Belprot/2230_TubePitotDeporte_v1.0.0/doc/Annexes/Mode d'emploi.pdf

## Mode d’emplois :

1. Branchez le connecteur de la baterie.
2. Vissez le support pile au boier principale.
3. Allumez le système à l’aide du switch.
4. Appairez le système à l’appareil Android.
5. Lancez l’applicaon dédiée.
