Belprot/2230_TubePitotDeporte_v1.0.0/doc/Annexes/Code/app.c.pdf

1 /******************************************************************************* 2 MPLAB Harmony Application Source File
3
4 | Company:
5 | Microchip Technology Inc.
6
7 | File Name:
8 | app.c
9
10 | Summary:
11 | This file contains the source code for the MPLAB Harmony application.
12
13 | Description:
14 | This file contains the source code for the MPLAB Harmony application. It
15 | implements the logic of the application's state machine and it may call
16 | API routines of other MPLAB Harmony modules in the system, such as drivers,
17 | system services, and middleware. However, it does not call any of the
18 | system interfaces (such as the "Initialize" and "Tasks" functions) of any of
19 | the modules in the system or make any assumptions about when those functions
20 | are called. That is the responsibility of the configuration-specific system
21 | files.
22 *******************************************************************************/ 23
24 // DOM-IGNORE-BEGIN
25 /******************************************************************************* 26 Copyright (c) 2013-2014 released Microchip Technology Inc. All rights reserved. 27
28 Microchip licenses to you the right to use, modify, copy and distribute
29 Software only when embedded on a Microchip microcontroller or digital signal 30 controller that is integrated into your product or third party product
31 (pursuant to the sublicense terms in the accompanying license agreement). 32
33 You should refer to the license agreement accompanying this Software for
34 additional information regarding your rights and obligations.
35
36 SOFTWARE AND DOCUMENTATION ARE PROVIDED "AS IS" WITHOUT WARRANTY OF ANY KIND, 37 EITHER EXPRESS OR IMPLIED, INCLUDING WITHOUT LIMITATION, ANY WARRANTY OF
38 MERCHANTABILITY, TITLE, NON-INFRINGEMENT AND FITNESS FOR A PARTICULAR PURPOSE. 39 IN NO EVENT SHALL MICROCHIP OR ITS LICENSORS BE LIABLE OR OBLIGATED UNDER
40 CONTRACT, NEGLIGENCE, STRICT LIABILITY, CONTRIBUTION, BREACH OF WARRANTY, OR 41 OTHER LEGAL EQUITABLE THEORY ANY DIRECT OR INDIRECT DAMAGES OR EXPENSES
42 INCLUDING BUT NOT LIMITED TO ANY INCIDENTAL, SPECIAL, INDIRECT, PUNITIVE OR 43 CONSEQUENTIAL DAMAGES, LOST PROFITS OR LOST DATA, COST OF PROCUREMENT OF
44 SUBSTITUTE GOODS, TECHNOLOGY, SERVICES, OR ANY CLAIMS BY THIRD PARTIES
45 (INCLUDING BUT NOT LIMITED TO ANY DEFENSE THEREOF), OR OTHER SIMILAR COSTS.
46 *******************************************************************************/ 47 // DOM-IGNORE-END
48

49
50 // Author M.Ricchieri
51
52
53 // ***************************************************************************** 54 // ***************************************************************************** 55 // Section: Included Files
56 // ***************************************************************************** 57 // ***************************************************************************** 58
59 #include "app.h"
60 #include "Mc32_I2cUtilCCS.h"
61
62 #include "HSCMRRN001PD2A3_driver.h" 63
64 #include "RN4678_driver.h"
65 #include "voltageADC_driver.h"
66
67
68
69 // ***************************************************************************** 70 // ***************************************************************************** 71 // Section: Global Data Definitions
72 // ***************************************************************************** 73 // *****************************************************************************
74

## C:/microchip/harmony/v2_06/apps/PROJ/2230_TubePitotDeporte_v1.0.0/firmware/src/app.c

1.1 of 6 | 2023.06.16 03:15:27

75 //----------------------------------------------------------------------------// Global data
76 APP_DATA | appData;
77 SENS_DATA | sensData;
78
79 struct inv_imu_device | myImuDevice;
80 struct inv_imu_serif | myImuSertif;
81
82
83
84 // ***************************************************************************** 85 // ***************************************************************************** 86 // Section: Application Callback Functions
87 // *****************************************************************************
88 // *****************************************************************************
89
90 ////----------------------------------------------------------------------------// TIMER0 callback function <--- Disabled 91 //void TIMER0_Callback_Function(){ //156Hz
92 //
93 // // xxxx
94 //}
95
96

97 //----------------------------------------------------------------------------// TIMER1 callback function 98 void TIMER1_Callback_Function(){ // 20Hz
99
100 // if(appData.isBluetoothDiscoverable){
101 //
102 // | if(inv_imu_get_time_us() >= 120000000){ // 120 000 000 = 120 seconds
103 //
104 // | turnOffDiscoverBT();
105 // | appData.isBluetoothDiscoverable = false;
106 // | }
107 // | }
108 | // Update the main state machine
109 | APP_UpdateAppState(APP_STATE_SERVICE);
110 }
111
112
113 //----------------------------------------------------------------------------// USART1_Callback_Function 114 void USART1_Callback_Function(void){
115
116 | char a_received[50];
117 | char* result;
118
119 | // Gets new data from FIFO
120 | getUsartData(&a_received[0]);
121
122 | // If "<RFCOMM_OPEN>" is present in the array received
123 | result = strstr(a_received, "<RFCOMM_OPEN>");
124 | if(result != NULL){
125
126 | appData.isBluetoothDiscoverable = false;
127 | appData.isBluetoothConnected = true;
128 | }
129
130 | // If "<RFCOMM_CLOSE>" is present in the array received
131 | result = strstr(a_received, "<RFCOMM_CLOSE>");
132 | if(result != NULL){
133
134 | // turnOnDiscoverBT();
135 | appData.isBluetoothConnected = false;
136 | }
137
138 // | // If "<xxxxxx>" is present in the array received
139 // | result = strstr(a_received, "<xxxxxx>");
140 // | if(result != NULL){
141 //
142 // | // Does something
143 // | }
144 }

145
146
147 //----------------------------------------------------------------------------// IMU callback function 148 void imu callback(inv imu sensor eventt *event){

_ | ( | _ | _ | _ | _ | ){

// Transforms 16bits values into degrees and saves them in the sensor data // structure
// 250 dps
sensData.gyroX = (event->gyro[0])/250 + 1; // + offset
sensData.gyroY = (event->gyro[1])/250 + 1; // + offset sensData.gyroZ = (event->gyro[2])/250;

// Reads and transforms 16bits values into
// Transforms 16bits values into g acceleration and saves them in the sensor // data structure (8192 bits per g)
sensData.accelX = (float)(event->accel[0])/8192.0;
sensData.accelY = (float)(event->accel[1])/8192.0;
sensData.accelZ = (float)(event->accel[2])/8192.0 + 0.075; // + offset

// Calculate the angle with the gyro values
// 0.05 correspond to the period between each reading 1/20Hz = 0.05s sensData.GyrAngleX += sensData.gyroX * 0.05;
sensData.GyrAngleY += sensData.gyroY * 0.05;
sensData.GyrAngleZ += sensData.gyroZ * 0.05;
169 }

172 // ***************************************************************************** 173 // ***************************************************************************** 174 // Section: Application Local Functions
175 // *****************************************************************************
176 // *****************************************************************************

178 //----------------------------------------------------------------------------// APP_UpdateAppState 179 void APP_UpdateAppState(APP_STATES newState){

appData.appState = newState;
182 }

185 //----------------------------------------------------------------------------// APP_UpdateServiceState 186 void APP_UpdateServiceState(SERVICE_STATES newState){

appData.serviceState = newState;
189 }

192 //----------------------------------------------------------------------------// clearArray

193 void clearArray(size_t arraySize, char *pArrayToClear){

int i;

for (i = 0; i < arraySize; i++){

pArrayToClear[i] = NULL;
}
201 }

204 //----------------------------------------------------------------------------// frameFormatting 205 inline void frameFormatting(char* a_dataToSend, const SENS_DATA* sensData){

// Saves all data into a simple frame
// Speed in [km/h]
// Gyros in [dps]
// Angles in [degrees]
// Accelerations in [g]
// VB and VG in [V]
sprintf(a_dataToSend, "S=%03d GX=%+.02f GY=%+.02f GZ=%+.02f GAX=%+.02f " "GAY=%+.02f GAZ=%+.02f AX=%+.02f AY=%+.02f AZ=%+.02f VB=%.02f " "VG=%.02f\n\r",
sensData->velocity,
sensData->gyroX, sensData->gyroY, sensData->gyroZ, sensData->GyrAngleX, sensData->GyrAngleY, sensData->GyrAngleZ, sensData->accelX, sensData->accelY, sensData->accelZ, sensData->batVoltage, sensData->genVoltage);
221 }

223 // ***************************************************************************** 224 // ***************************************************************************** 225 // Section: Application Initialization and State Machine Functions
226 // *****************************************************************************
227 // *****************************************************************************
228
229 //----------------------------------------------------------------------------// APP_Initialize 230 void APP_Initialize(void){
231
232 // Initializes the appData structure
233
234 | appData.appState | = APP_STATE_INIT;
235 | appData.isBluethoothModuleInit = false;
236 | appData.isBluetoothConnected | = false;
237 | appData.isBluetoothDiscoverable = false;
238 | sensData.GyrAngleX = 0;
239 | sensData.GyrAngleY = 0;
240 | sensData.GyrAngleZ = 0;

241 }
242
243
244 //----------------------------------------------------------------------------// initImuInterface 245 // Initialize serial interface between MCU and IMU
246 int initImuInterface(struct inv_imu_serif *icm_serif){
247
248 | // No need
249 icm_serif->context | = 0;
250 | // Points to the reading function dedicated
251 icm_serif->read_reg | = ICM42670P_I2C_bus_read;
252 | // Points to the writing function dedicated
253 icm_serif->write_reg = ICM42670P_I2C_bus_write;
254 icm_serif->max_read = 255; /* maximum number of bytes allowed per serial read */ 255 icm_serif->max_write = 255; /* maximum number of bytes allowed per serial write */ 256 // Set the communication interface
257 icm_serif->serif_type = SERIF_TYPE;
258
259 return 0;
260 }
261
262
263 //----------------------------------------------------------------------------// APP_Tasks 264 void APP_Tasks(void){
265
266 RAW_ADC rawAdc;
267
268 | // Check the application's current state
269 | switch(appData.appState){
270
271 | // Application's initial state
272 | case APP_STATE_INIT:
273 | {
274 | int rc = 0;
275
276 | // Initialization of the I2C communication
277 | i2c_init(SLOW);
278
279 | do{
280 | // Initialization of the ICM42670 interface
281 | rc |= initImuInterface(&myImuSertif);
282 | // Resets and prepares the chip for the configuration
283 | rc |= setupImuDevice(&myImuSertif);
284 | // Configures ICM42670 parameters
285 | rc |= configureImuDevice();
286
287 | }while(rc != INV_ERROR_SUCCESS);
288
289 | // Initialization of the USART FIFOs
290 | initFifo(&usartFifoRx, FIFO_RX_SIZE, a_fifoRx, 0);
291 | initFifo(&usartFifoTx, FIFO_TX_SIZE, a_fifoTx, 0);
292
293 | do{
294 | // Initialization of the Bluetooth module
295 | appData.isBluethoothModuleInit = init_RN4678();
296

}while(appData.isBluethoothModuleInit == false);

// Initialization of the ADC module
initAdc();

// Starts TIMERs
303 // | DRV_TMR0_Start(); <--- Disabled
| DRV_TMR1_Start();
| DRV_TMR2_Start();
| // States machines update
| APP_UpdateAppState(APP_STATE_WAIT);
| APP_UpdateServiceState(SERVICE_STATE_READ_SENSORS);
| break;
}
| case APP_STATE_SERVICE:
{
| int8_t a_frameToSend[130];
| switch(appData.serviceState){
| case SERVICE_STATE_READ_SENSORS:
| // Reads voltages values
| readRawAdc(&rawAdc);
| convertRawToVoltage(&rawAdc, &sensData);
| // Reads velocity value
| convertRawToVelocity(readRawDiffPress(), &sensData);
| // Gets new IMU data
| get_imu_data();

APP_UpdateServiceState(SERVICE_STATE_PROCESS); break;

case SERVICE_STATE_PROCESS:

// Clears the array before saving new values

clearArray(sizeof(a_frameToSend), (char*)&a_frameToSend[0]); // Converts float values in a char array (frame) frameFormatting((char*)&a_frameToSend[0], &sensData);

APP_UpdateServiceState(SERVICE_STATE_SEND_DATA_BT); break;

case SERVICE_STATE_SEND_DATA_BT:

// Bluetooth is connected to a device if(appData.isBluetoothConnected == true){

// Sends frame through USART sendData_RN4678(&a_frameToSend[0]); // Toggle signalisation LED SIGN_LEDToggle();
}
else SIGN_LEDOn();

APP_UpdateAppState(APP_STATE_WAIT); APP_UpdateServiceState(SERVICE_STATE_READ_SENSORS); break;
}
break;
}

case APP_STATE_WAIT:
{
// Does nothing here
break;
}
default:
{
// Does nothing here

370 | // Does nothing here
371 | break;
372 | }
373 | }
374 }
375
376
377 /******************************************************************************* 378 End of File
379 */
