Belprot/2230_TubePitotDeporte_v1.0.0/doc/Annexes/Code/HSCMRRN001PD2A3_driver.c.pdf

1 /*
2 * File: HSCMRRN001PD2A3_driver.c 3 * Author: M.Ricchieri
4 *
5 * Created on 12. avril 2023
6 */

9 //----------------------------------------------------------------------------// Includes 10 #include "HSCMRRN001PD2A3_driver.h"
11 #include "math.h"
12 #include "Mc32_I2cUtilCCS.h"
13 #include "peripheral\i2c\plib_i2c.h"

16 //----------------------------------------------------------------------------// Constants 17 #define HSCMRRN001PD2A3_ADDR 0x51

19 #define RHO_AIR 1.2

22 //----------------------------------------------------------------------------// readRawDiffPress 23 // Read the raw compensed differential pressure from the HSCMRRN001PD2A3 sensor
24 int16_t readRawDiffPress(){

int16_t rawDiffPress;
uint8_t MSB;
uint8_t LSB;

// I2C communication with the sensor i2c_start();
i2c_write(HSCMRRN001PD2A3_ADDR);
MSB = i2c_read(1);
LSB = i2c_read(1);
// Reads 2 unused bytes to avoid bug // needs to be clarified ! i2c_read(1);
i2c_read(0); // No ACK
i2c_stop();

// Data formatting
rawDiffPress = MSB;
rawDiffPress = rawDiffPress << 8;
rawDiffPress = rawDiffPress | LSB;
rawDiffPress = rawDiffPress - 8192; // Safety to avoid negative speeds if(rawDiffPress < 0) rawDiffPress = 0;

return rawDiffPress;

49 }

52 //----------------------------------------------------------------------------// convertRawToVelocity 53 // Convert raw compensed differential pressure to velocity (km/h))
54 void convertRawToVelocity(int16_t rawDiffPress, SENS_DATA *pSensData){

// Multiplied by 3.6 to obtain velocity in km/h instead of m/s pSensData->velocity = 3.6 * (sqrtf((2*(float)rawDiffPress)/(RHO_AIR))); 58 }

C:/microchip/harmony/v2_06/apps/PROJ/2230_TubePitotDeporte_v1.0.0/firmware/src/HSCMRRN001PD2A3_driver.c

1.1 of 1 | 2023.06.15 00:41:27
