Belprot/2230_TubePitotDeporte_v1.0.0/doc/Annexes/Code/I2C_ICM42670P_Functions.c.pdf

2 /*
3 * File: I2C_ICM42670P_Function.c 4 * Author: M.Ricchieri
5 *
6 * Created on 10. mai 2023
7 *
8 * This code uses the Mc32_I2cUtilCCS.h 9 */

12 //----------------------------------------------------------------------------// Includes 13 #include "stdint.h"
14 #include "Mc32_I2cUtilCCS.h"
15 #include "imu/inv_imu_driver.h"
16 #include "imu/inv_imu_transport.h" 17 #include "I2C_ICM42670P_Functions.h"

20 //----------------------------------------------------------------------------// Constants 21 #define ICM42670P_INIT_VALUE 0
22 #define I2C_BUFFER_LEN 10
23 #define ICM42670P_I2C_BUS_WRITE_ARRAY_INDEX 1

26 // \Brief : Those functions are used by the ICM42670 IMU to communicate with
27 // | the chip in I2C. The first one is used to read and the second to
28 // | write in the chip. Those functions are pointed by the ICM42670
29 // | driver.

31 //----------------------------------------------------------------------------// ICM42670P_I2C_bus_write 32 int ICM42670P_I2C_bus_write(struct inv_imu_serif *serif, uint8_t reg,
| const uint8_t *buf, uint32_t len){
| int cursor = 0;
| i2c_start();
| i2c_write(ICM42670P_ADDR_W);
| i2c_write(reg);
| for (cursor = 0; cursor < len; cursor++){
| i2c_write(*(buf+cursor));
}
| i2c_stop();
| return 0;
48 }

51 //----------------------------------------------------------------------------// ICM42670P_I2C_bus_read 52 int ICM42670P_I2C_bus_read(struct inv_imu_serif *serif, uint8_t reg,
uint8_t *buf, uint32_t len){

uint8_t array[len];
int cursor = 0;

i2c_start();
i2c_write(ICM42670P_ADDR_W); i2c_write(reg);
i2c_start();
i2c_write(ICM42670P_ADDR_R);

for (cursor = 0; cursor < len; cursor++){

if((cursor+1) < len)
// With ACK
array[cursor] = i2c_read(1); else
// Without ACK
array[cursor] = i2c_read(0);

buf[cursor] = array[cursor]; //*(buf+cursor) = array[cursor];

C:/microchip/harmony/v2_06/apps/PROJ/2230_TubePitotDeporte_v1.0.0/firmware/src/I2C_ICM42670P_Functions.c

1.1 of 2 | 2023.06.15 00:41:27

75 | }
76 | i2c_stop();
77
78 return 0;
79 }

C:/microchip/harmony/v2_06/apps/PROJ/2230_TubePitotDeporte_v1.0.0/firmware/src/I2C_ICM42670P_Functions.c

2.1 of 2 | 2023.06.15 00:41:27
