Belprot/2230_TubePitotDeporte_v1.0.0/doc/Annexes/Code/TerminalFragment.java.pdf

1 | package de.kai_morich.simple_bluetooth_terminal;
3 | import android.annotation.SuppressLint;
4 | import android.app.Activity;
5 | import android.app.AlertDialog;
6 | import android.bluetooth.BluetoothAdapter;
7 | import android.bluetooth.BluetoothDevice;
8 | import android.content.ComponentName;
9 | import android.content.Context;
10 | import android.content.Intent;
11 | import android.content.ServiceConnection;
12 | import android.os.Bundle;
13 | import android.os.IBinder;
14 | import android.text.Spannable;
15 | import android.text.SpannableStringBuilder;
16 | import android.text.style.ForegroundColorSpan;
17 | import android.view.LayoutInflater;
18 | import android.view.Menu;
19 | import android.view.MenuInflater;
20 | import android.view.MenuItem;
21 | import android.view.View;
22 | import android.view.ViewGroup;
23 | import android.widget.TextView;
24 | import android.widget.Toast;
25
26 | import androidx.annotation.NonNull;
27 | import androidx.annotation.Nullable;
28 | import androidx.fragment.app.Fragment;
29
30 | import java.util.ArrayDeque;
31 | import static java.lang.Math.*;
32
33
34
35 | public class TerminalFragment extends Fragment implements ServiceConnection,
SerialListener {
36
37 | private enum Connected { False, Pending, True }
38
39 | private String deviceAddress;
40 | private SerialService service;
41
42 | //private TextView receiveText;
43
44 | private TextView speedText;
45 | private TextView gyroXText;
46 | private TextView gyroYText;
47 | private TextView gyroZText;
48 | private TextView anglGyrXText;
49 | private TextView anglGyrYText;
50 | private TextView anglGyrZText;
51 | private TextView accelXText;
52 | private TextView accelYText;
53 | private TextView accelZText;
54 | private TextView vbatText;
55 | private TextView vgenText;
56 | private TextView pitchText;
57 | private TextView yawText;
58 | private TextView rollText;
59
60
61 | private TextView sendText;
62 | private TextUtil.HexWatcher hexWatcher;
64 | private Connected connected = Connected.False;
65 | private boolean initialStart = true;

66 | private boolean hexEnabled = false;
67 | private boolean pendingNewline = false;
68 | private String newline = TextUtil.newline_crlf;
70 | // Personal variables
71 | public double sValue = 0.0;
72 | public double gxValue = 0.0;
73 | public double gyValue = 0.0;
74 | public double gzValue = 0.0;
75 | public double gaxValue = 0.0;
76 | public double gayValue = 0.0;
77 | public double gazValue = 0.0;
78 | public double axValue = 0.0;
79 | public double ayValue = 0.0;
80 | public double azValue = 0.0;
81 | public double vbatValue = 0.0;
82 | public double vgenValue = 0.0;
83
84 | /*
85 | * Lifecycle
86 | */
87 | @Override
88 | public void onCreate(@Nullable Bundle savedInstanceState){
89 | super.onCreate(savedInstanceState);
90 | setHasOptionsMenu(true);
91 | setRetainInstance(true);
92 | deviceAddress = getArguments().getString("device");
93 | }
94
95 | @Override
96 | public void onDestroy() {
97 | if (connected != Connected.False)
98 | disconnect();
99 | getActivity().stopService(new Intent(getActivity(), SerialService.class));
100 | super.onDestroy();
101 | }
102
103 | @Override
104 | public void onStart() {
105 | super.onStart();
106 | if(service != null)
107 | service.attach(this);
108 | else
109 | getActivity().startService(new Intent(getActivity(), SerialService.class));
| // prevents service destroy on unbind from recreated activity caused by
| orientation change
110 | }
111
112 | @Override
113 | public void onStop() {
114 | if(service != null && !getActivity().isChangingConfigurations())
115 | service.detach();
116 | super.onStop();
117 | }
118
119 | @SuppressWarnings("deprecation") // onAttach(context) was added with API 23.
| onAttach(activity) works for all API versions
120 | @Override
121 | public void onAttach(@NonNull Activity activity){
122 | super.onAttach(activity);
123 | getActivity().bindService(new Intent(getActivity(), SerialService.class), this,
| Context.BIND_AUTO_CREATE);
126 | @Override
127 | public void onDetach() {

128 | try { getActivity().unbindService(this); } catch(Exception ignored) {}
129 | super.onDetach();
132 | @Override
133 | public void onResume() {
134 | super.onResume();
135 | if(initialStart && service != null){
136 | initialStart = false;
137 | getActivity().runOnUiThread(this::connect);
138 | }
139 | }
140
141 | @Override
142 | public void onServiceConnected(ComponentName name, IBinder binder){
143 | service = ((SerialService.SerialBinder) binder).getService();
144 | service.attach(this);
145 | if(initialStart && isResumed()) {
146 | initialStart = false;
147 | getActivity().runOnUiThread(this::connect);
148 | }
149 | }
150
151 | @Override
152 | public void onServiceDisconnected(ComponentName name){
153 | service = null;
154 | }
155
156 | /*
157 | * UI
158 | */
159 | @Override
160 | public View onCreateView(@NonNull LayoutInflater inflater, ViewGroup container,
| Bundle savedInstanceState){
161 | View view = inflater.inflate(R.layout.fragment_terminal, container, false);
162 | // Assignment text to textView
163 | speedText = view.findViewById(R.id.speed_viewer);
164 | gyroXText = view.findViewById(R.id.gyroX_viewer);
165 | gyroYText = view.findViewById(R.id.gyroY_viewer);
166 | gyroZText = view.findViewById(R.id.gyroZ_viewer);
167 | anglGyrXText = view.findViewById(R.id.angGyrX_viewer);
168 | anglGyrYText = view.findViewById(R.id.angGyrY_viewer);
169 | anglGyrZText = view.findViewById(R.id.angGyrZ_viewer);
170 | accelXText = view.findViewById(R.id.accelX_viewer);
171 | accelYText = view.findViewById(R.id.accelY_viewer);
172 | accelZText = view.findViewById(R.id.accelZ_viewer);
173 | vbatText = view.findViewById(R.id.vbat_viewer);
174 | vgenText = view.findViewById(R.id.vgen_viewer);
175 | pitchText = view.findViewById(R.id.pitch_viewer);
176 | yawText = view.findViewById(R.id.yaw_viewer);
177 | rollText = view.findViewById(R.id.roll_viewer);
178
179 | //receiveText = view.findViewById(R.id.receive_text);
| // TextView performance decreases with number of spans
180 | //receiveText.setTextColor(getResources().getColor(R.color.colorRecieveText));
| // set as default color to reduce number of spans
181 | //receiveText.setMovementMethod(ScrollingMovementMethod.getInstance());
182
183 | sendText = view.findViewById(R.id.send_text);
184 | hexWatcher = new TextUtil.HexWatcher(sendText);
185 | hexWatcher.enable(hexEnabled);
186 | sendText.addTextChangedListener(hexWatcher);
187 | sendText.setHint(hexEnabled ? "HEX mode" : "");
189 | View sendBtn = view.findViewById(R.id.send_btn);
190 | sendBtn.setOnClickListener(v -> send(sendText.getText().toString()));

191 | return view;
194 | @Override
195 | public void onCreateOptionsMenu(@NonNull Menu menu, MenuInflater inflater){
196 | inflater.inflate(R.menu.menu_terminal, menu);
197 | menu.findItem(R.id.hex).setChecked(hexEnabled);
198 | }
199
200 | @Override
201 | public boolean onOptionsItemSelected(MenuItem item){
202 | int id = item.getItemId();
203 | if (id == R.id.clear){
204 | //receiveText.setText("");
205 | return true;
206 | } else if (id == R.id.newline){
207 | String[] newlineNames = getResources().getStringArray(R.array.newline_names);
208 | String[] newlineValues = getResources().getStringArray(R.array.newline_values
| );
209 | int pos = java.util.Arrays.asList(newlineValues).indexOf(newline);
210 | AlertDialog.Builder builder = new AlertDialog.Builder(getActivity());
211 | builder.setTitle("Newline");
212 | builder.setSingleChoiceItems(newlineNames, pos,(dialog, item1) -> {
213 | newline = newlineValues[item1];
214 | dialog.dismiss();
215 | });
216 | builder.create().show();
217 | return true;
218 | } else if (id == R.id.hex){
219 | hexEnabled =!hexEnabled;
220 | sendText.setText("");
221 | hexWatcher.enable(hexEnabled);
222 | sendText.setHint(hexEnabled ? "HEX mode" : "");
223 | item.setChecked(hexEnabled);
224 | return true;
225 | } else {
226 | return super.onOptionsItemSelected(item);
227 | }
228 | }
229
230 | /*
231 | * Serial + UI
232 | */
233 | private void connect() {
234 | try {
235 | BluetoothAdapter bluetoothAdapter = BluetoothAdapter.getDefaultAdapter();
236 | BluetoothDevice device = bluetoothAdapter.getRemoteDevice(deviceAddress);
237 | status("connecting...");
238 | connected = Connected.Pending;
239 | SerialSocket socket = new SerialSocket(getActivity().getApplicationContext(),
| device);
240 | service.connect(socket);
241 | } catch (Exception e){
242 | onSerialConnectError(e);
243 | }
244 | }
245
246 | private void disconnect() {
247 | connected = Connected.False;
248 | service.disconnect();
249 | }
250
251 | private void send(String str){
252 | if(connected != Connected.True){
253 | Toast.makeText(getActivity(), "not connected", Toast.LENGTH_SHORT).show();
254 | return;

256 | try {
257 | String msg;
258 | byte[] data;
259 | if(hexEnabled){
260 | StringBuilder sb = new StringBuilder();
261 | TextUtil.toHexString(sb, TextUtil.fromHexString(str));
262 | TextUtil.toHexString(sb, newline.getBytes());
263 | msg = sb.toString();
264 | data = TextUtil.fromHexString(msg);
265 | } else {
266 | msg = str;
267 | data =(str + newline).getBytes();
268 | }
269 | SpannableStringBuilder spn = new SpannableStringBuilder(msg + '\n');
270 | spn.setSpan(new ForegroundColorSpan(getResources().getColor(R.color.
| colorSendText)), 0, spn.length(), Spannable.SPAN_EXCLUSIVE_EXCLUSIVE);
271 | //receiveText.append(spn);
272 | service.write(data);
273 | } catch (Exception e){
274 | onSerialIoError(e);
275 | }
276 | }
277
278 | @SuppressLint("SetTextI18n")
279 | private void receive(ArrayDeque<byte[]> datas){
280 | SpannableStringBuilder spn = new SpannableStringBuilder();
281 | for (byte[] data : datas){
282 | if (hexEnabled){
283 | spn.append(TextUtil.toHexString(data)).append('\n');
284 | } else {
285 | String msg = new String(data);
286 | if (newline.equals(TextUtil.newline_crlf) && msg.length() > 0){
287 | // don't show CR as ^M if directly before LF
288 | msg = msg.replace(TextUtil.newline_crlf, TextUtil.newline_lf);
289 | // special handling if CR and LF come in separate fragments
290 | if (pendingNewline && msg.charAt(0) == '\n'){
291 | if (spn.length() >= 2){
292 | spn.delete(spn.length() - 2, spn.length());
293 | } else {
294 | //Editable edt = receiveText.getEditableText();
295 | //if (edt != null && edt.length() >= 2)
296 | // edt.delete(edt.length() - 2, edt.length());
297 | }
298 | }
299 | pendingNewline = msg.charAt(msg.length() - 1) == '\r';
300 | }
301 | spn.append(TextUtil.toCaretString(msg, newline.length() != 0));
302 | }
303 | }
304
| //-------------------------------------------------------------------------------
| ---------// PERSONAL
305
306 | String[] pairs = spn.toString().split("\\s+"); | // Séparer la chaîne en paires
| clé-valeur
307
308 | for (String pair : pairs){
309 | String[] parts = pair.split("="); // Séparer chaque paire clé-valeur
310
311 | if (parts.length == 2){
312 | String key = parts[0];
313 | String valueStr = parts[1];
315 | try {
316 | double value = Double.parseDouble(valueStr);

318 | switch (key){
319 | case "S":
320 | sValue = value;
321 | break;
322 | case "GX":
323 | gxValue = value;
324 | break;
325 | case "GY":
326 | gyValue = value;
327 | break;
328 | case "GZ":
329 | gzValue = value;
330 | break;
331 | case "GAX":
332 | gaxValue = value;
333 | break;
334 | case "GAY":
335 | gayValue = value;
336 | break;
337 | case "GAZ":
338 | gazValue = value;
339 | break;
340 | case "AX":
341 | axValue = value;
342 | break;
343 | case "AY":
344 | ayValue = value;
345 | break;
346 | case "AZ":
347 | azValue = value;
348 | break;
349 | case "VB":
350 | vbatValue = value;
351 | break;
352 | case "VG":
353 | vgenValue = value;
354 | break;
355
356 | }
357 | } catch (NumberFormatException e){
358 | | // Gérer l'exception si la valeur n'est pas un nombre décimal valide
359 | }
360 | }
361 | }
362
363
364 | speedText.setText( "SPEED : " + String.valueOf(sValue)+ " km/h");
365 | gyroXText.setText( "GYRO X : " + String.valueOf(gxValue)+ " dps");
366 | gyroYText.setText( "GYRO Y : " + String.valueOf(gyValue)+ " dps");
367 | gyroZText.setText( "GYRO Z : " + String.valueOf(gzValue)+ " dps");
368 | anglGyrXText.setText("ANGL GYR X : " + String.valueOf(gaxValue)+ " °");
369 | anglGyrYText.setText("ANGL GYR Y : " + String.valueOf(gayValue)+ " °");
370 | anglGyrZText.setText("ANGL GYR Z : " + String.valueOf(gazValue)+ " °");
371 | accelXText.setText( "ACCEL X : " + String.valueOf(axValue)+ " g");
372 | accelYText.setText( "ACCEL Y : " + String.valueOf(ayValue)+ " g");
373 | accelZText.setText( "ACCEL Z : " + String.valueOf(azValue)+ " g");
374 | vbatText.setText( "VBAT : " + String.valueOf(vbatValue)+ " V");
375 | vgenText.setText( "VGEN : " + String.valueOf(vgenValue)+ " V");
376
377 | // Calculation of angles
378 | //pitchValue = Math.atan(axValue/(Math.sqrt(Math.pow(ayValue, 2) +
| Math.pow(azValue, 2))));
380 | //double angle = atan2(ayValue, axValue); // Calcul de l'angle en radians

382 | //double angle = atan(axValue/ayValue);
383 | // Conversion de l'angle en degrés et en float
384 | //float pitchValue = (float) toDegrees(angle);
386 | // Calcul des angles
387 | double roll = Math.atan2(ayValue, azValue);
388 | double pitch = Math.atan2(-axValue, Math.sqrt(ayValue * ayValue + azValue *
| azValue));
389 | double yaw = Math.atan2(Math.sin(roll)* axValue - Math.cos(roll)* ayValue, Math
| .cos(roll)* azValue);
390
391 | // Conversion des angles en degrés
392 | //roll = Math.toDegrees(roll);
393 | pitch = Math.toDegrees(pitch);
394 | yaw = Math.toDegrees(yaw);
395
396 | pitchText.setText( "PITCH : " + String.format("%.2f", pitch)+ " °");
397 | yawText.setText( "YAW : " + String.format("%.2f", yaw)+ " °");
398 | //rollText.setText( "ROLL : " + String.format("%.2f", roll) + " °");
399
400
401 | /*
402 | receiveText.append("Speed = " + sValue + " km/h" + " GyroX = " + gxValue + "
| GyroY = " + gyValue +
403 | " GyroZ = " + gzValue + " AccelX = " + axValue + " AccelY = " + ayValue
| +
404 | " AccelZ = " + azValue + " Vbat = " + vbatValue + " Vgen = " +
| vgenValue + '\n');
405 | */
406
407
| //-------------------------------------------------------------------------------
| ---------//
408
409 | //receiveText.append(spn);
410 | }
411
412
413 | private void status(String str){
414 | SpannableStringBuilder spn = new SpannableStringBuilder(str + '\n');
415 | spn.setSpan(new ForegroundColorSpan(getResources().getColor(R.color.
| colorStatusText)), 0, spn.length(), Spannable.SPAN_EXCLUSIVE_EXCLUSIVE);
416 | //receiveText.append(spn);
417 | }
418
419 | /*
420 | * SerialListener
421 | */
422 | @Override
423 | public void onSerialConnect() {
424 | status("connected");
425 | connected = Connected.True;
426 | }
427
428 | @Override
429 | public void onSerialConnectError(Exception e){
430 | status("connection failed: " + e.getMessage());
431 | disconnect();
432 | }
433
434 | @Override
435 | public void onSerialRead(byte[] data){
436 | ArrayDeque<byte[]> datas = new ArrayDeque<>();
437 | datas.add(data);
438 | receive(datas);

441 | public void onSerialRead(ArrayDeque<byte[]> datas){
442 | receive(datas);
445 | @Override
446 | public void onSerialIoError(Exception e){
447 | status("connection lost: " + e.getMessage());
448 | disconnect();
449 | }
450
451 | }
452
