Belprot/2230_TubePitotDeporte_v1.0.0/doc/Diagrammes/CodeC/SM.jpg

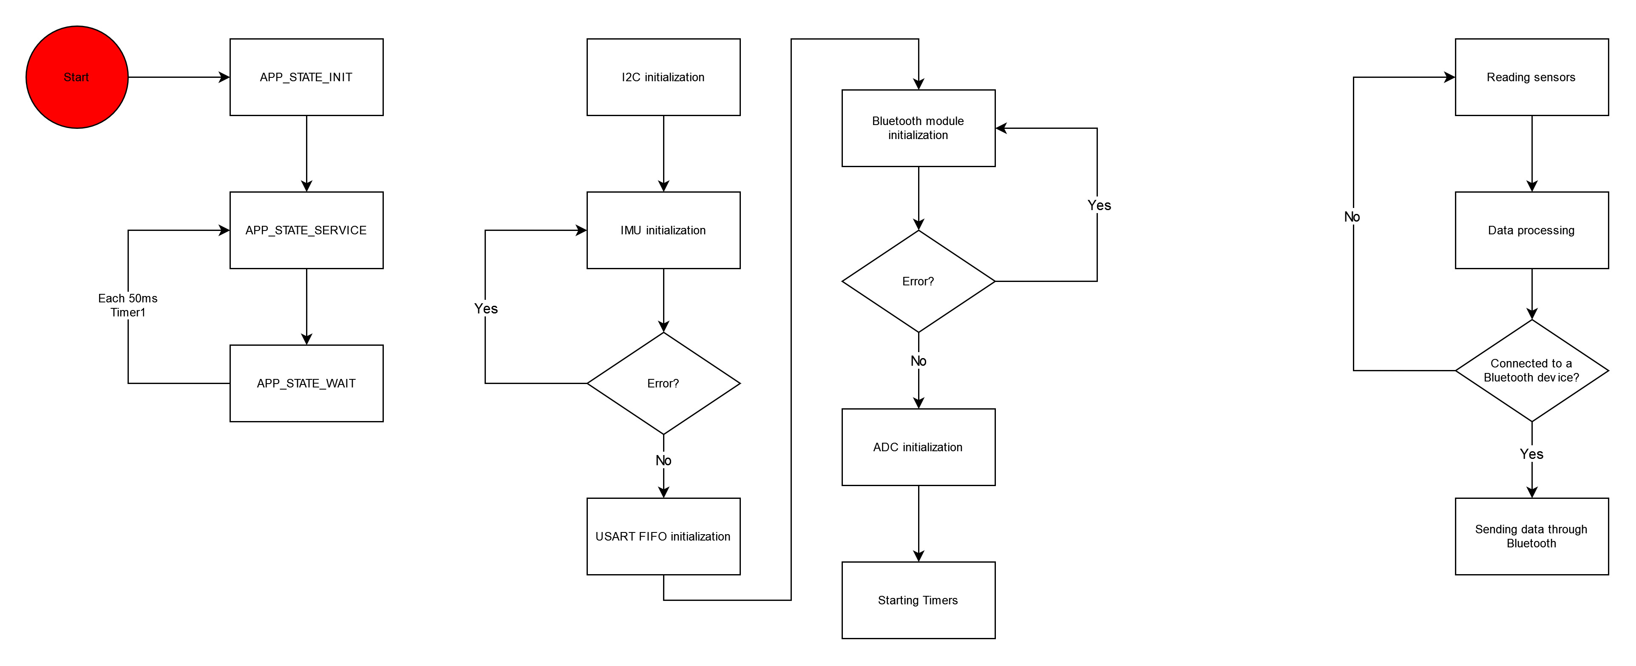
doc/Diagrammes/CodeC/SM.jpg
