Belprot/2230_TubePitotDeporte_v1.0.0/doc/Diagrammes/SchemaBlocRapport_v1.0.0.png

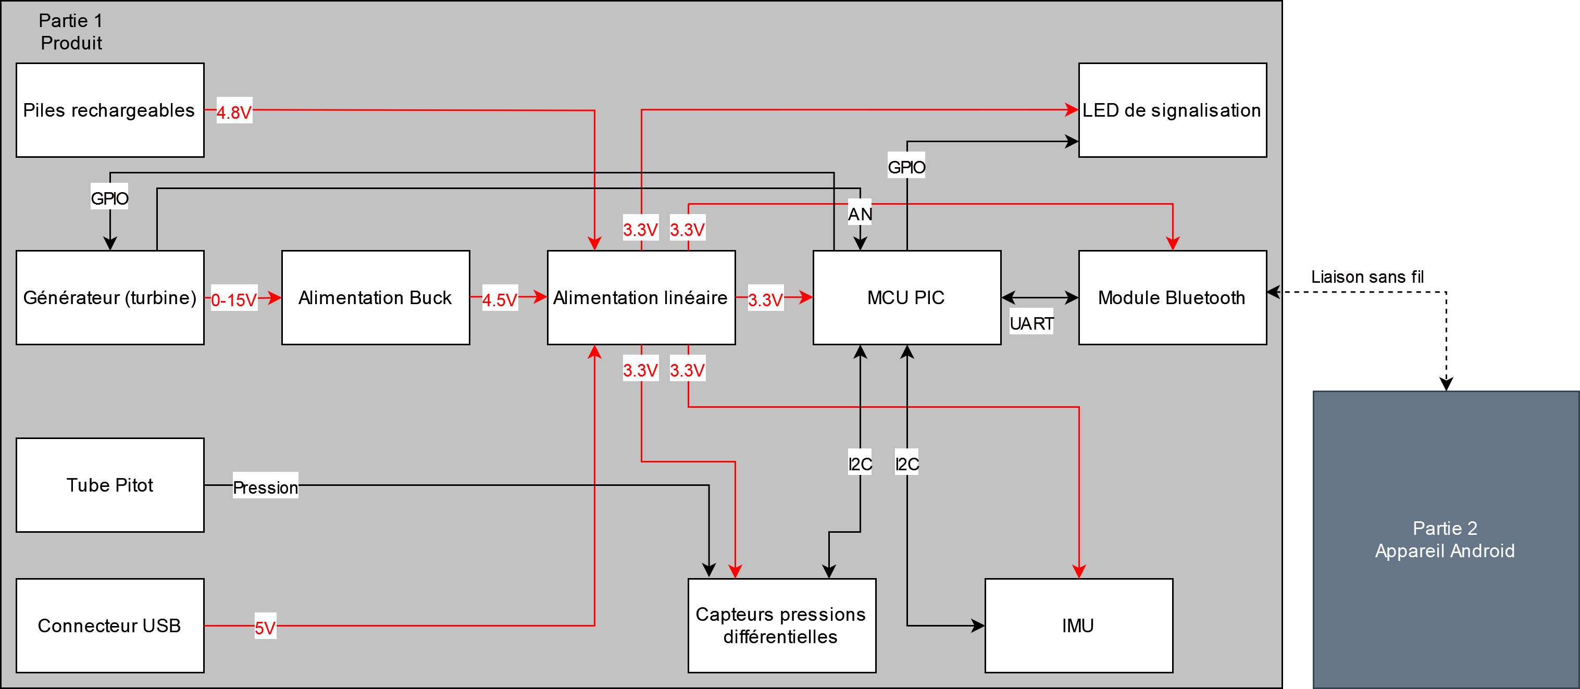
doc/Diagrammes/SchemaBlocRapport_v1.0.0.png
