Belprot/2230_TubePitotDeporte_v1.0.0/doc/Images/Autre/12-Cessna140A-HBCOR-2005-071_AMPA.jpg

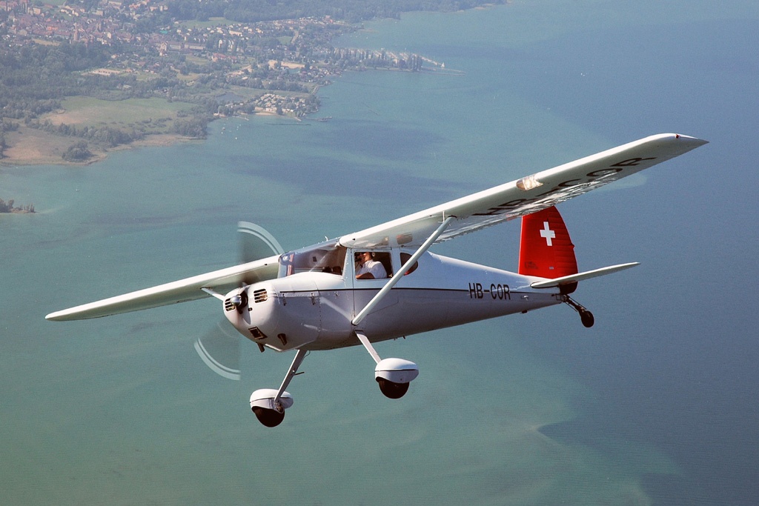
doc/Images/Autre/12-Cessna140A-HBCOR-2005-071_AMPA.jpg
