Belprot/2230_TubePitotDeporte_v1.0.0/doc/Images/Autre/CroquisMecanique.PNG

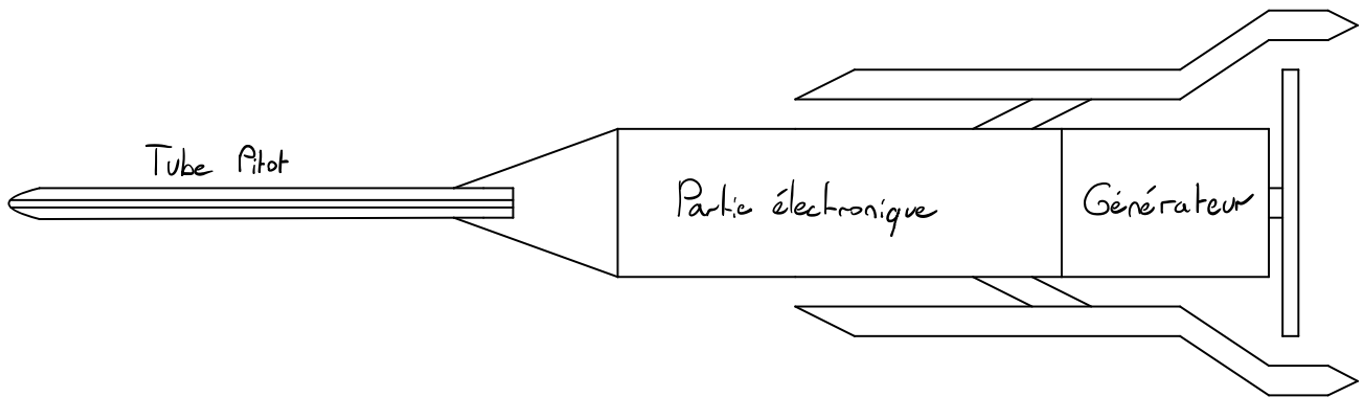
doc/Images/Autre/CroquisMecanique.PNG
