Belprot/2230_TubePitotDeporte_v1.0.0/doc/Images/Autre/EstimationPrixPre-Etude.PNG

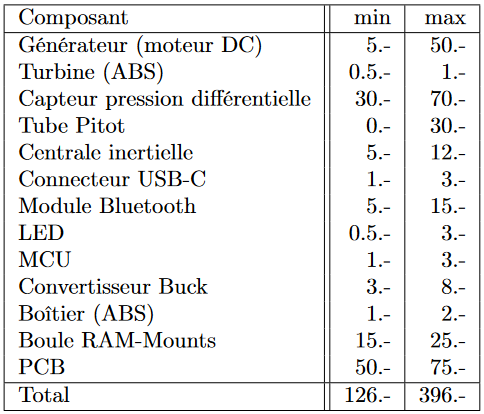
doc/Images/Autre/EstimationPrixPre-Etude.PNG
