Belprot/2230_TubePitotDeporte_v1.0.0/doc/Images/Autre/IMU_assiette.PNG

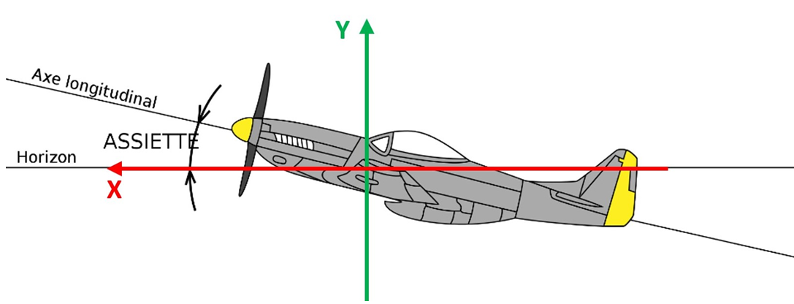
doc/Images/Autre/IMU_assiette.PNG
