Belprot/2230_TubePitotDeporte_v1.0.0/doc/Images/Autre/piper-cub-j-3-3.png

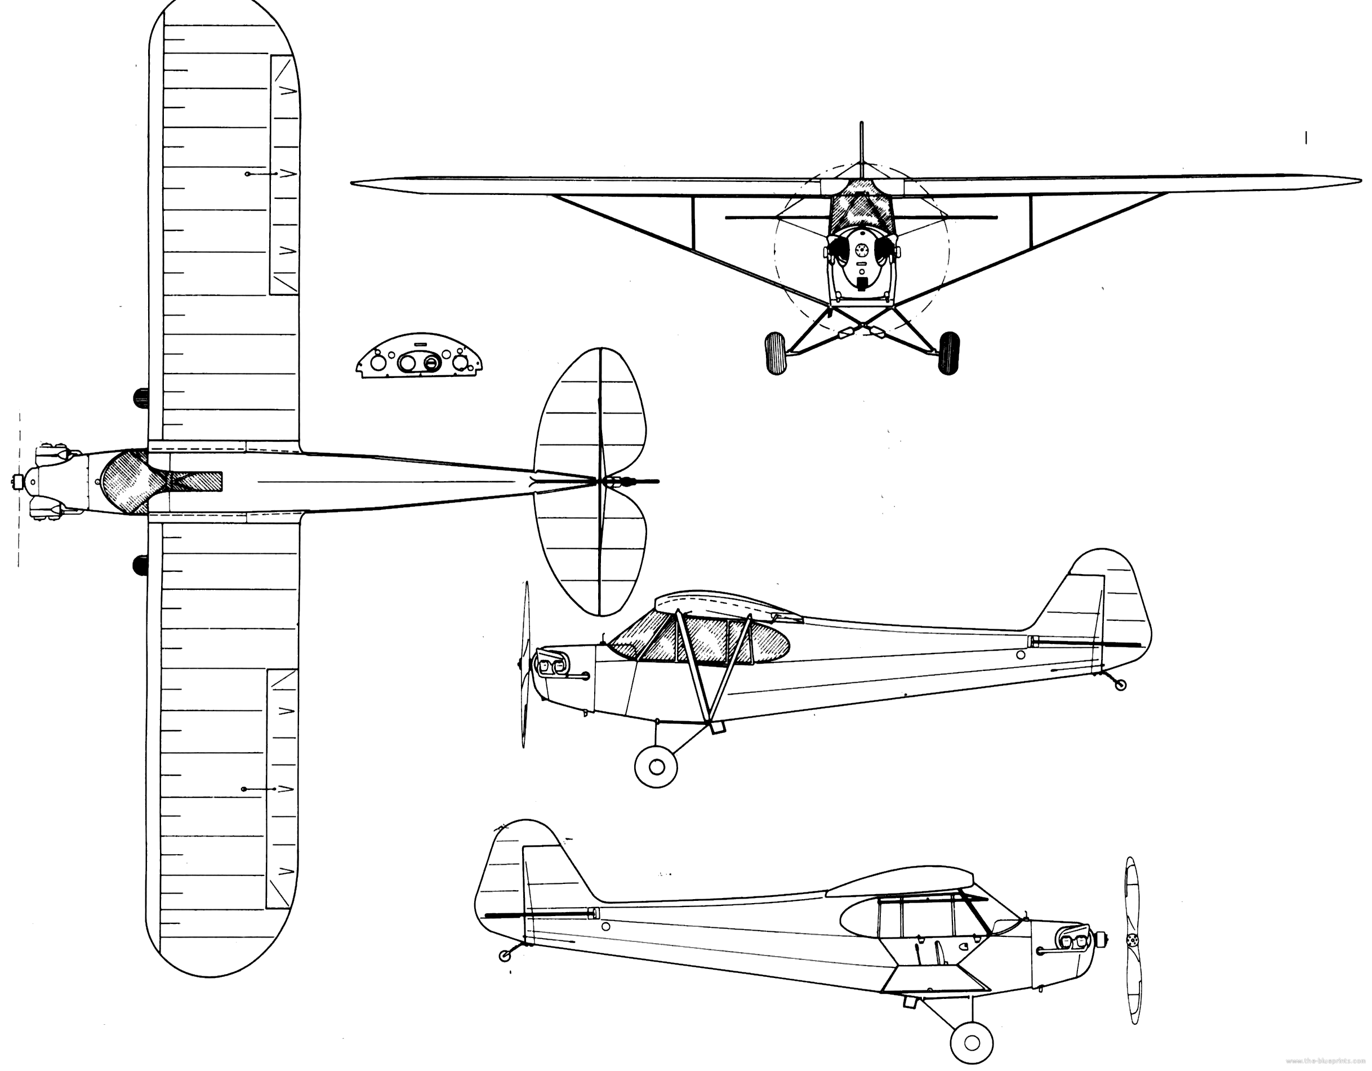
doc/Images/Autre/piper-cub-j-3-3.png
