Belprot/2230_TubePitotDeporte_v1.0.0/doc/Images/Autre/piper-cub-j-3-3_modified.PNG

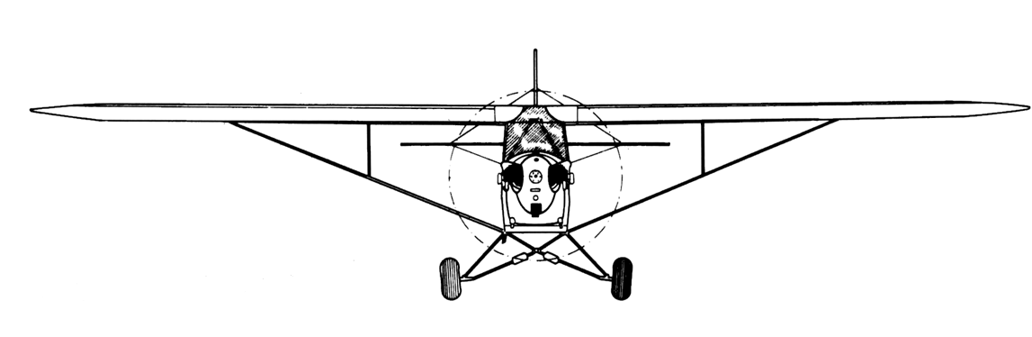
doc/Images/Autre/piper-cub-j-3-3_modified.PNG
