Belprot/2230_TubePitotDeporte_v1.0.0/doc/Images/Autre/TubePitot.PNG

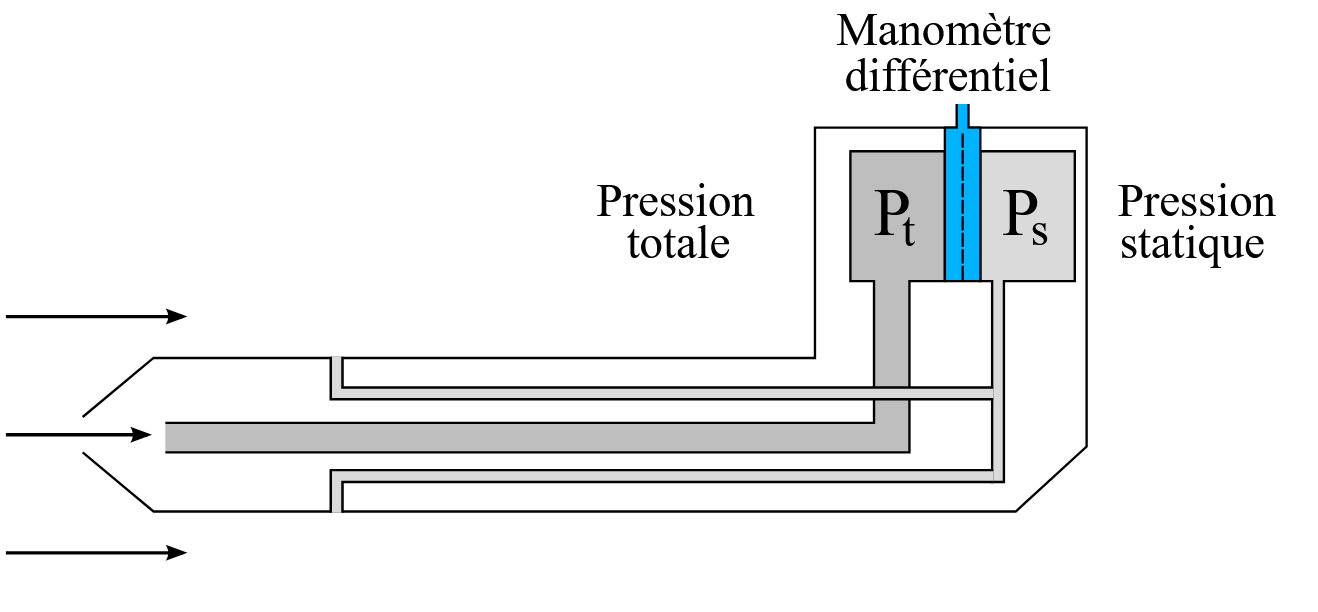
doc/Images/Autre/TubePitot.PNG
