Belprot/2230_TubePitotDeporte_v1.0.0/doc/Images/Autre/TubesPitot.PNG.jpg

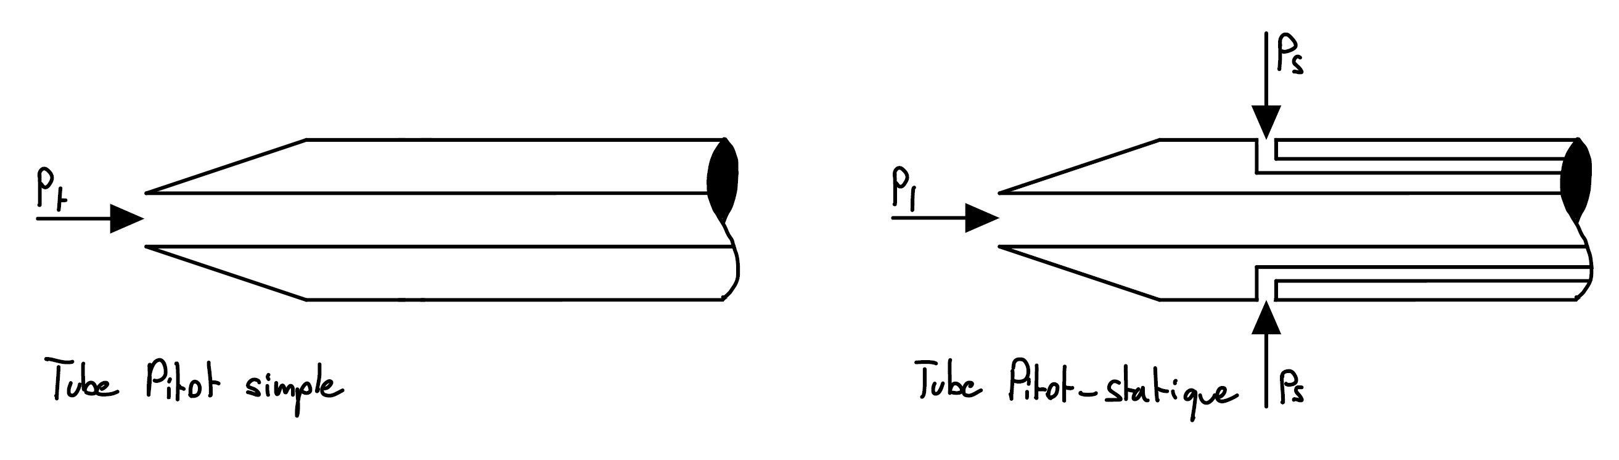
doc/Images/Autre/TubesPitot.PNG.jpg
