Belprot/2230_TubePitotDeporte_v1.0.0/doc/images/DesignElec/173950536.PNG

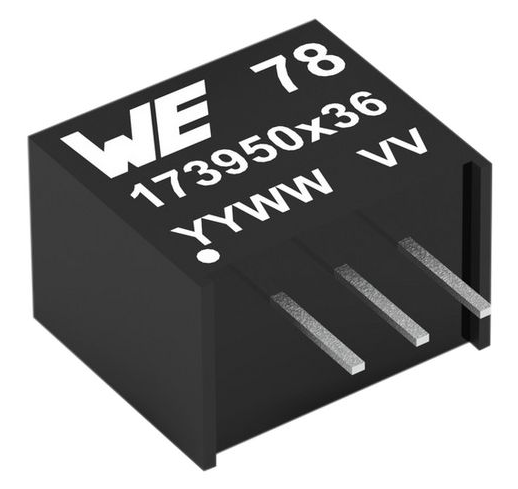
doc/images/DesignElec/173950536.PNG
