Belprot/2230_TubePitotDeporte_v1.0.0/doc/images/DesignElec/AlimLin_SCH.PNG

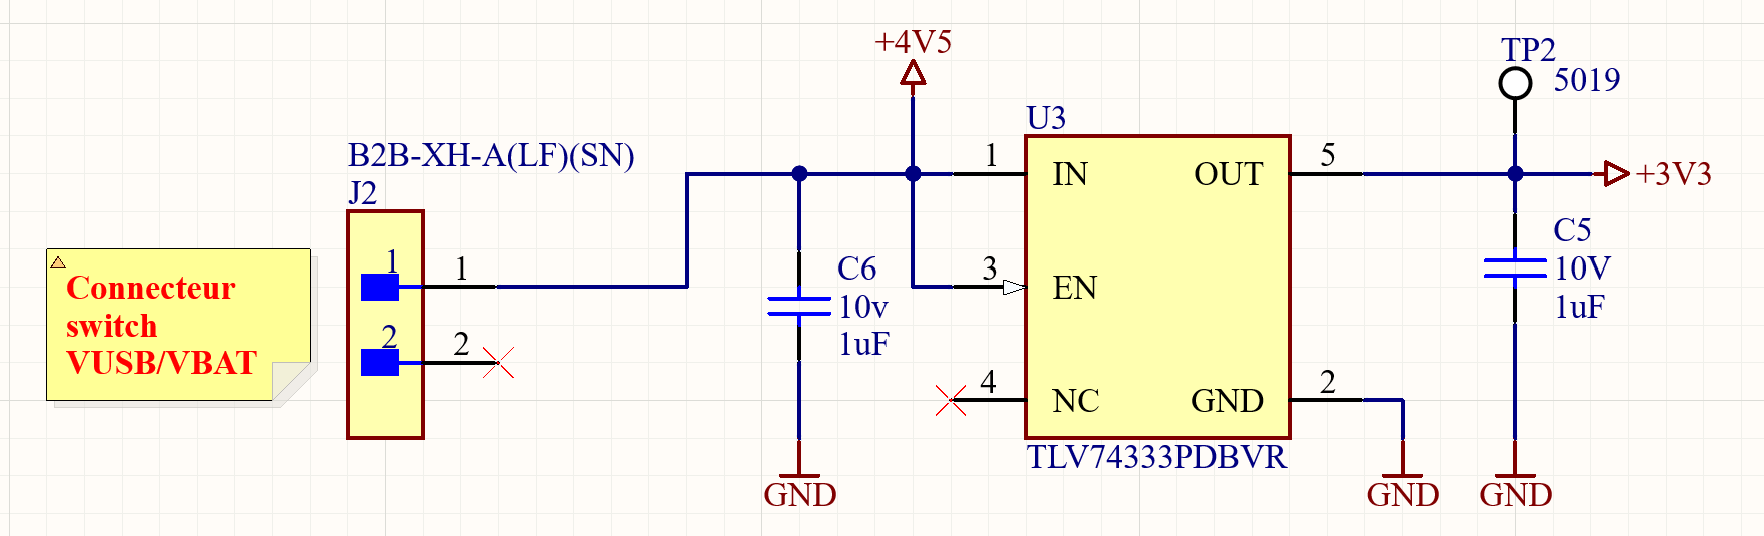
doc/images/DesignElec/AlimLin_SCH.PNG
