Belprot/2230_TubePitotDeporte_v1.0.0/doc/images/DesignElec/ConnectUSBC_SCH.PNG

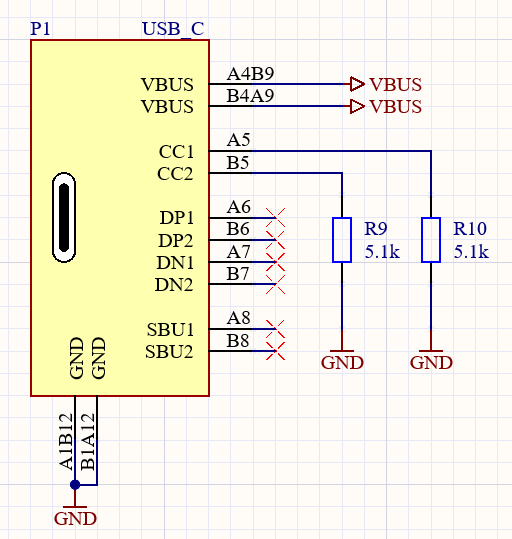
doc/images/DesignElec/ConnectUSBC_SCH.PNG
