Belprot/2230_TubePitotDeporte_v1.0.0/doc/images/DesignElec/ConnPiles_SCH.PNG

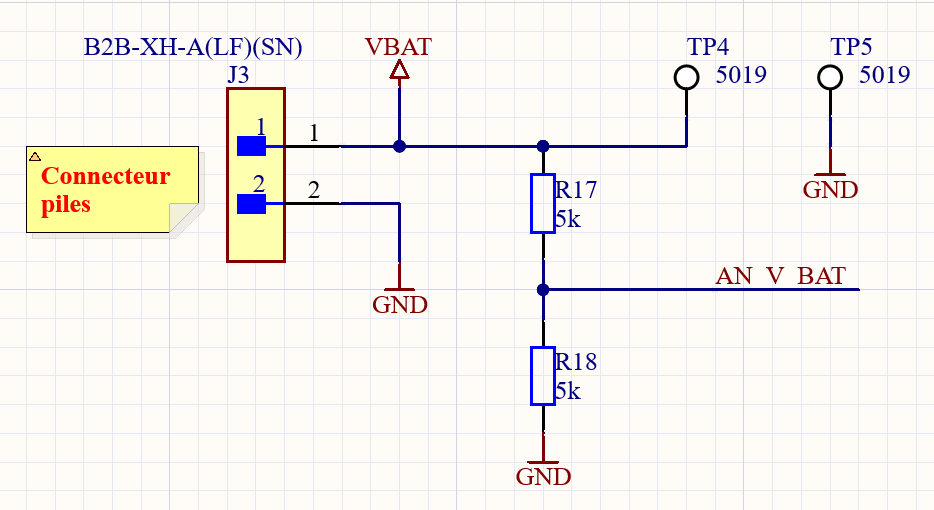
doc/images/DesignElec/ConnPiles_SCH.PNG
