Belprot/2230_TubePitotDeporte_v1.0.0/doc/images/DesignElec/OscillateurExt_SCH.PNG

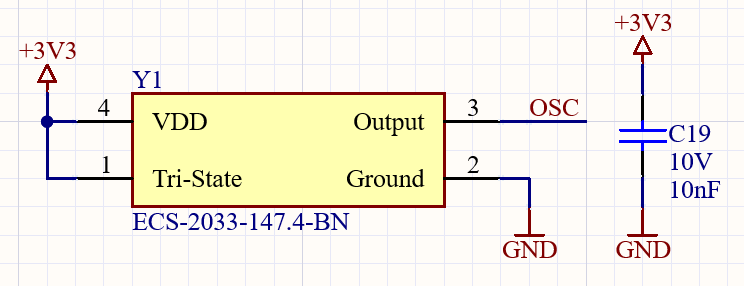
doc/images/DesignElec/OscillateurExt_SCH.PNG
