Belprot/2230_TubePitotDeporte_v1.0.0/doc/images/DesignElec/PIC32MX.png

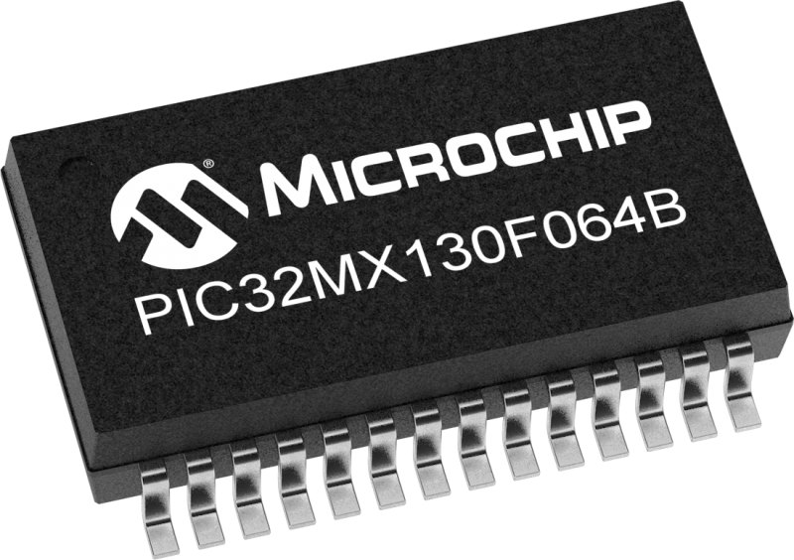
doc/images/DesignElec/PIC32MX.png
