Belprot/2230_TubePitotDeporte_v1.0.0/doc/images/DesignElec/PilesRechargeables.PNG

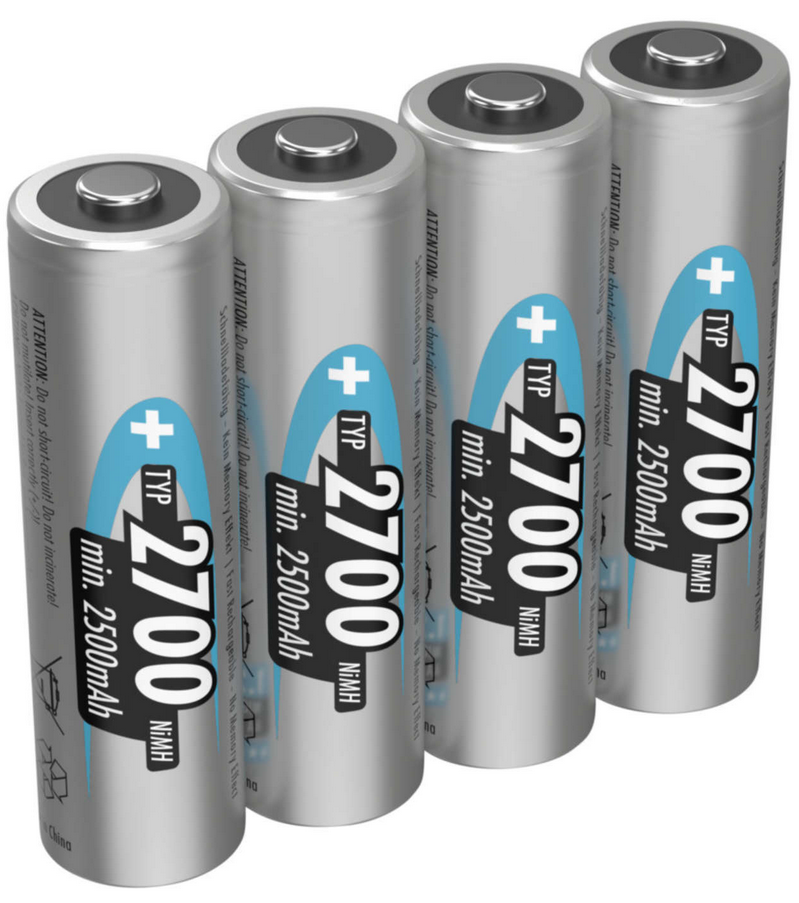
doc/images/DesignElec/PilesRechargeables.PNG
