Belprot/2230_TubePitotDeporte_v1.0.0/doc/images/DesignElec/PuissanceVoltageCurrent.PNG

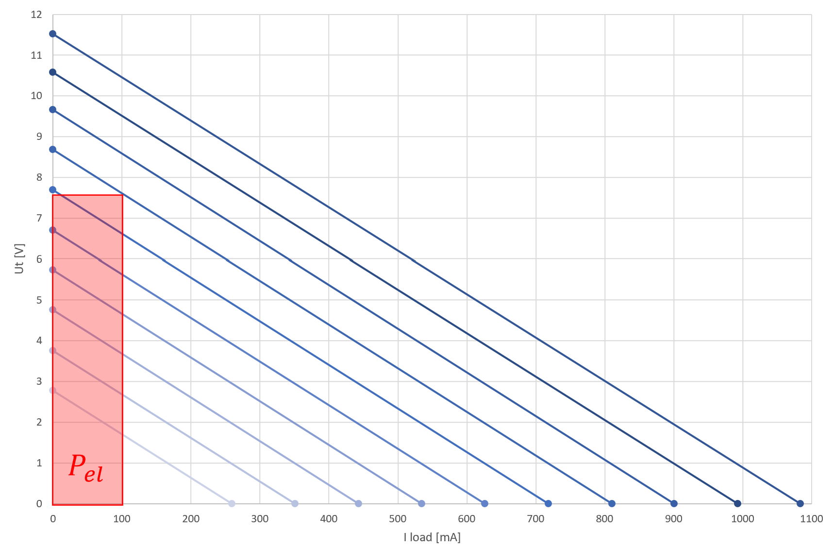
doc/images/DesignElec/PuissanceVoltageCurrent.PNG
