Belprot/2230_TubePitotDeporte_v1.0.0/doc/images/DesignElec/RF-370A-15370.PNG

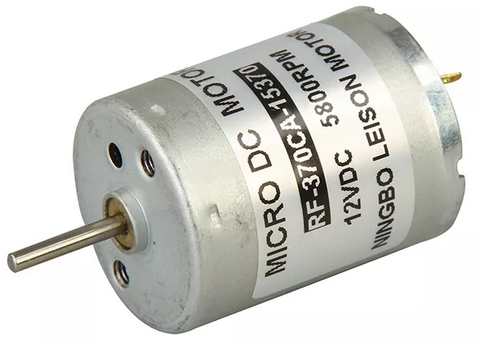
doc/images/DesignElec/RF-370A-15370.PNG
