Belprot/2230_TubePitotDeporte_v1.0.0/doc/images/DesignElec/TLV74333PDBVR.PNG

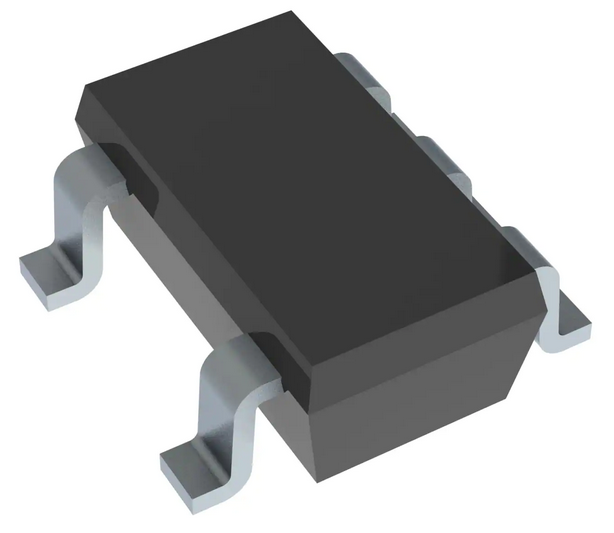
doc/images/DesignElec/TLV74333PDBVR.PNG
