Belprot/2230_TubePitotDeporte_v1.0.0/doc/images/DesignMecEtPCB/bot.jpg

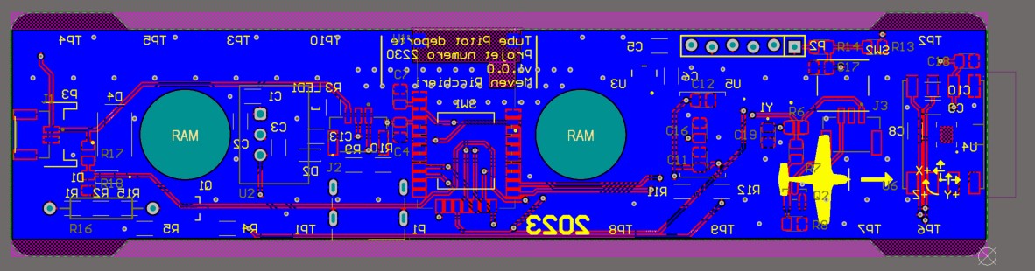
doc/images/DesignMecEtPCB/bot.jpg
