Belprot/2230_TubePitotDeporte_v1.0.0/doc/images/DesignMecEtPCB/RAM-Mounts.jpg

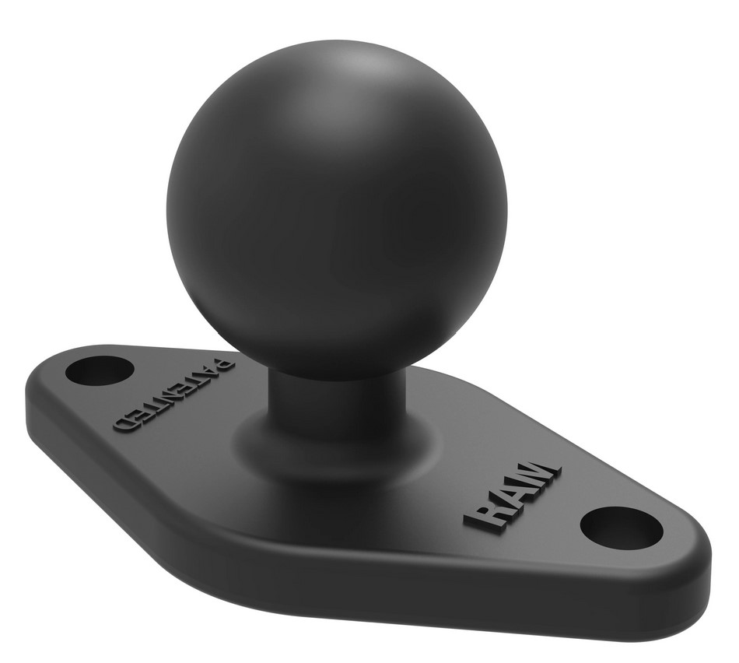
doc/images/DesignMecEtPCB/RAM-Mounts.jpg
