Belprot/2230_TubePitotDeporte_v1.0.0/doc/images/DesignMecEtPCB/Top.jpg

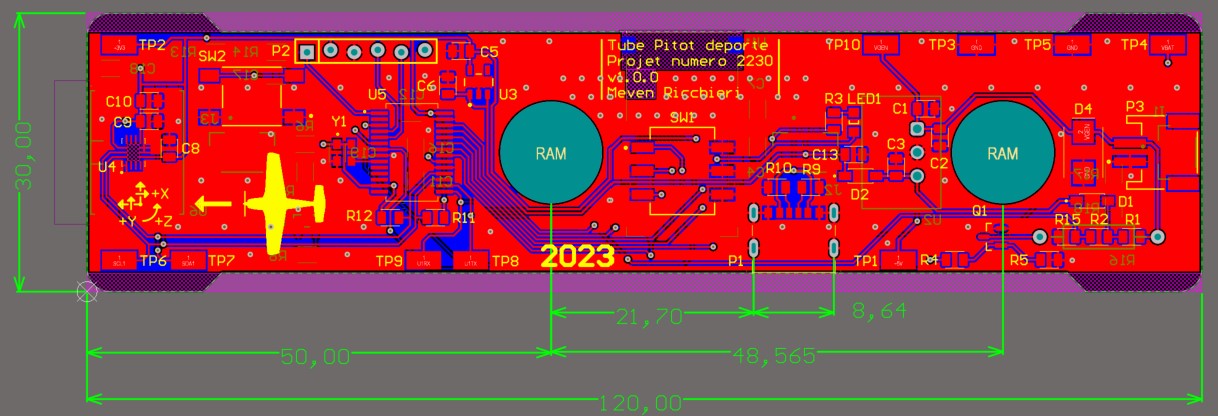
doc/images/DesignMecEtPCB/Top.jpg
