Belprot/2230_TubePitotDeporte_v1.0.0/doc/images/DesignMecEtPCB/TubePitotCommande.png

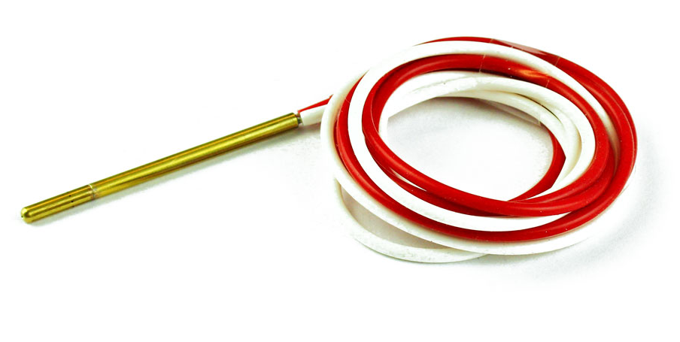
doc/images/DesignMecEtPCB/TubePitotCommande.png
