Belprot/2230_TubePitotDeporte_v1.0.0/doc/Images/Mesures/bitI2C.jpg

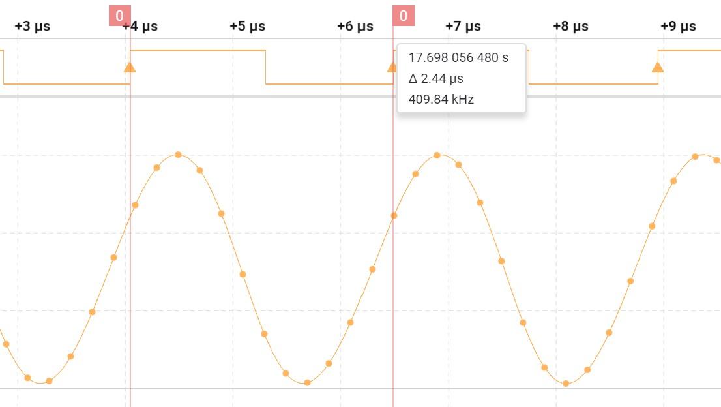
doc/Images/Mesures/bitI2C.jpg
