Belprot/2230_TubePitotDeporte_v1.0.0/doc/images/Mesures/SchemaMesureAlim.jpg

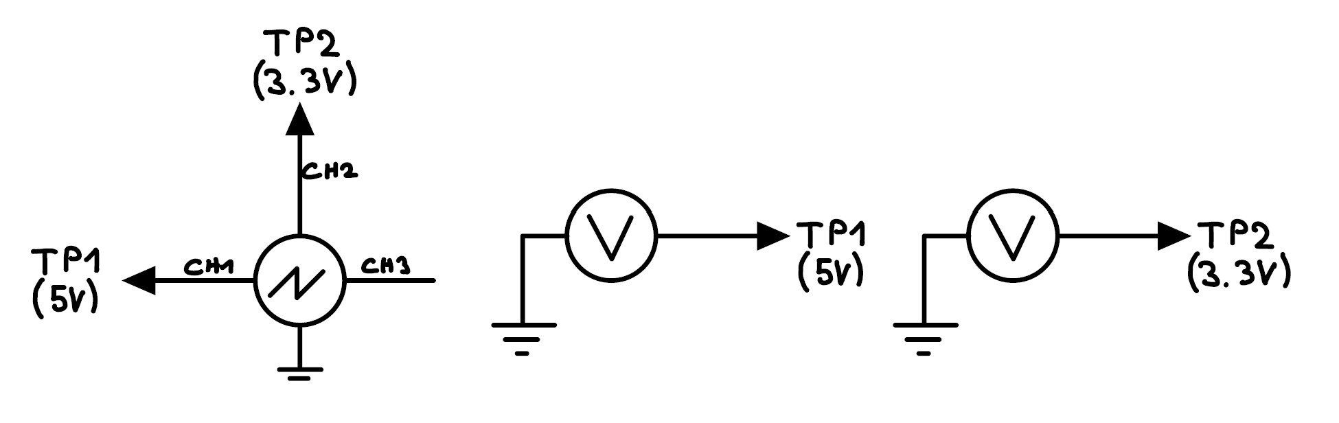
doc/images/Mesures/SchemaMesureAlim.jpg
