Belprot/2230_TubePitotDeporte_v1.0.0/doc/images/Mesures/Timer1.jpg

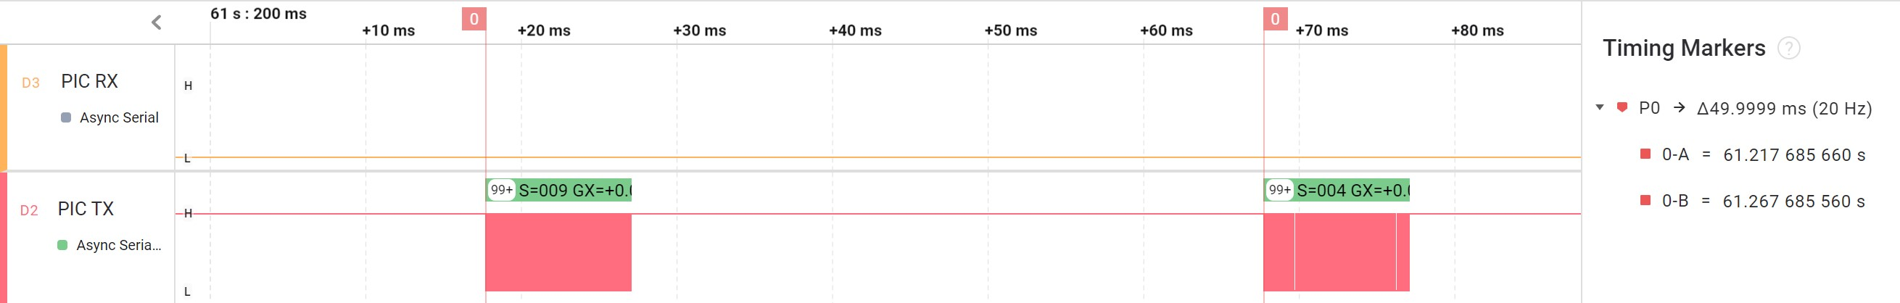
doc/images/Mesures/Timer1.jpg
