Belprot/2230_TubePitotDeporte_v1.0.0/doc/Images/Mesures/Timer1_2.jpg

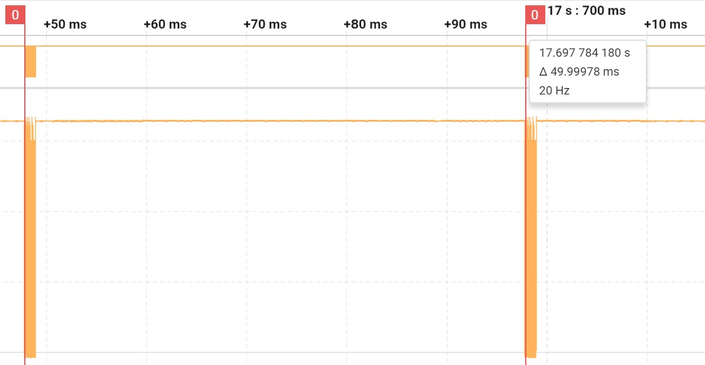
doc/Images/Mesures/Timer1_2.jpg
