Belprot/2230_TubePitotDeporte_v1.0.0/doc/Images/Mesures/TrameI2C.jpg

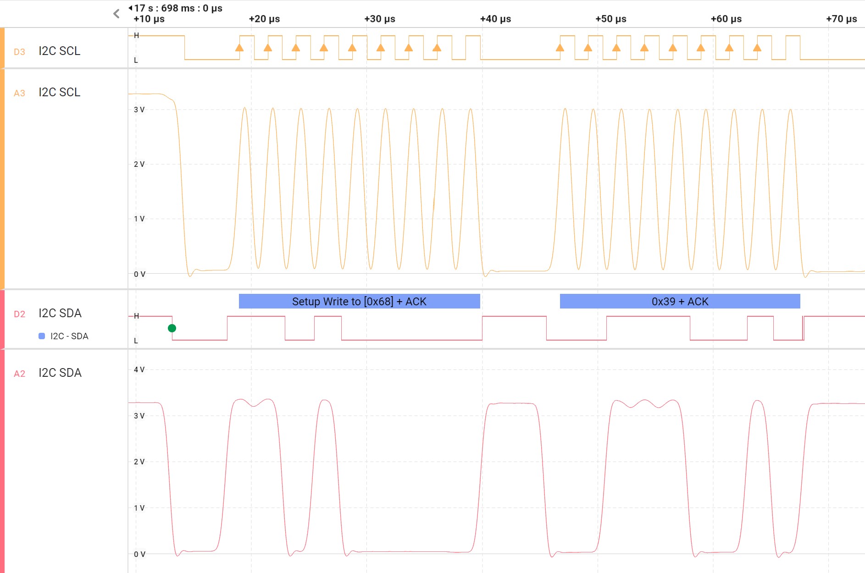
doc/Images/Mesures/TrameI2C.jpg
