Belprot/2230_TubePitotDeporte_v1.0.0/doc/Images/Mesures/TrameI2C_SLOW.jpg

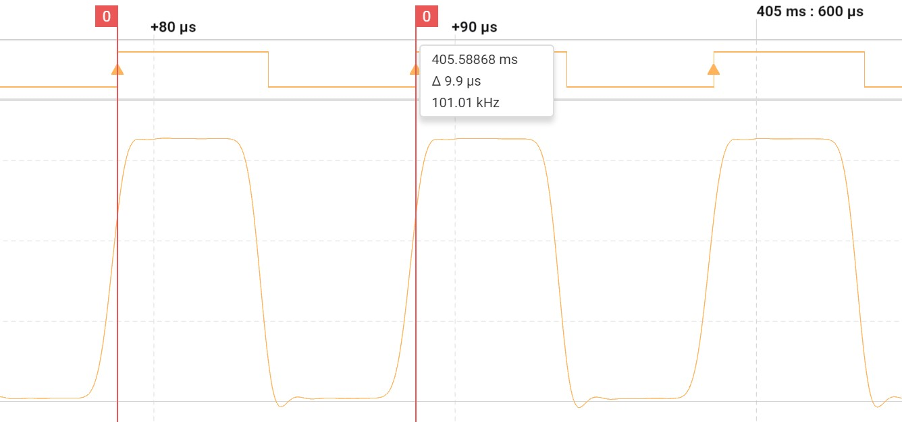
doc/Images/Mesures/TrameI2C_SLOW.jpg
