Belprot/2230_TubePitotDeporte_v1.0.0/doc/images/Mesures/TrameUSART.jpg

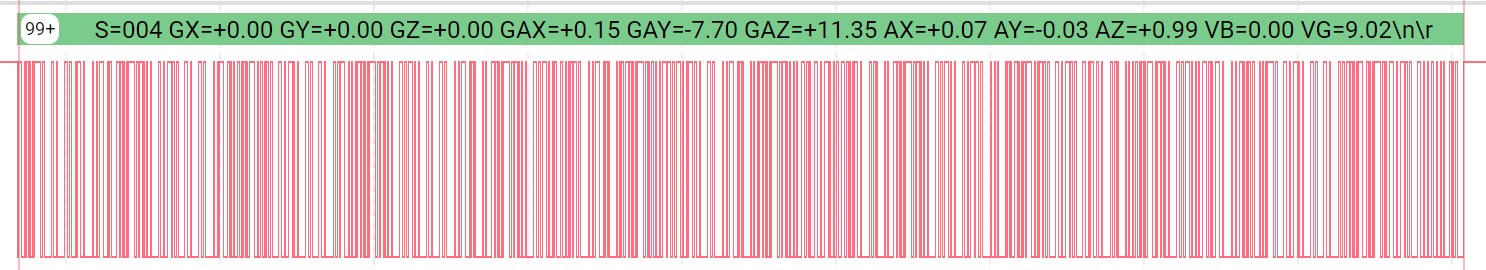
doc/images/Mesures/TrameUSART.jpg
