Belprot/2230_TubePitotDeporte_v1.0.0/doc/Images/Mesures/USART_TrameSSS.jpg

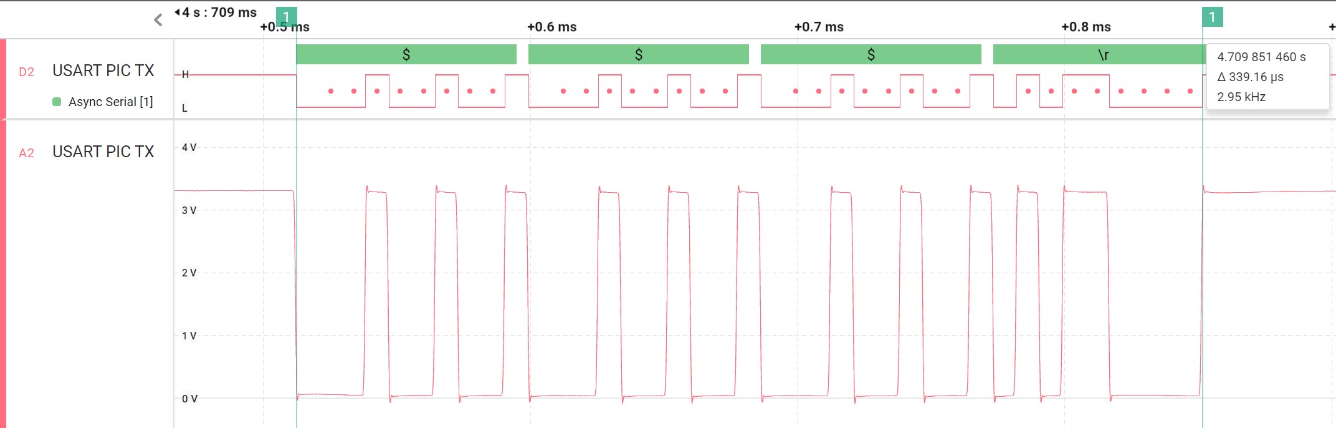
doc/Images/Mesures/USART_TrameSSS.jpg
