Belprot/2230_TubePitotDeporte_v1.0.0/doc/Images/North_American_F-100_Super_Sabre_silhouette.svg.png

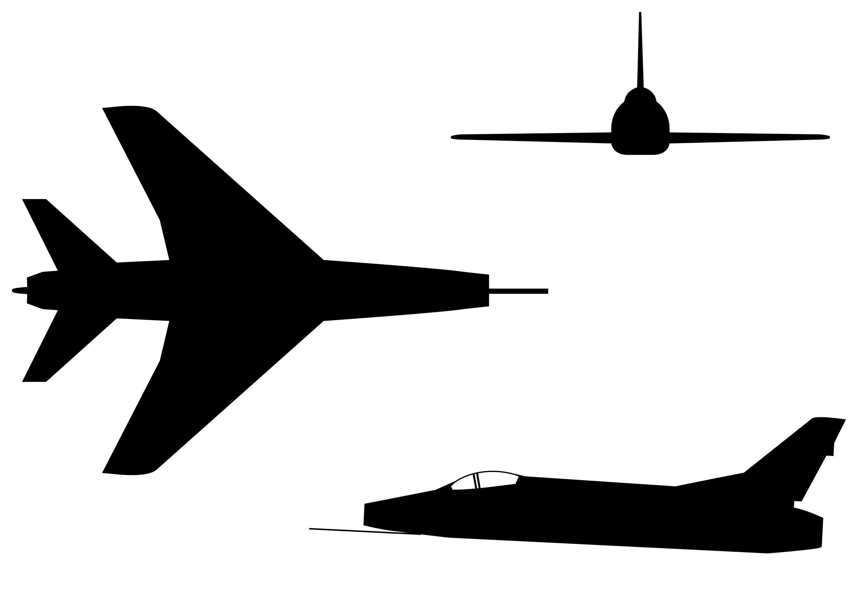
doc/Images/North_American_F-100_Super_Sabre_silhouette.svg.png
