Belprot/2230_TubePitotDeporte_v1.0.0/doc/Images/PhotosProjetTerminé/IMG_2862.jpg

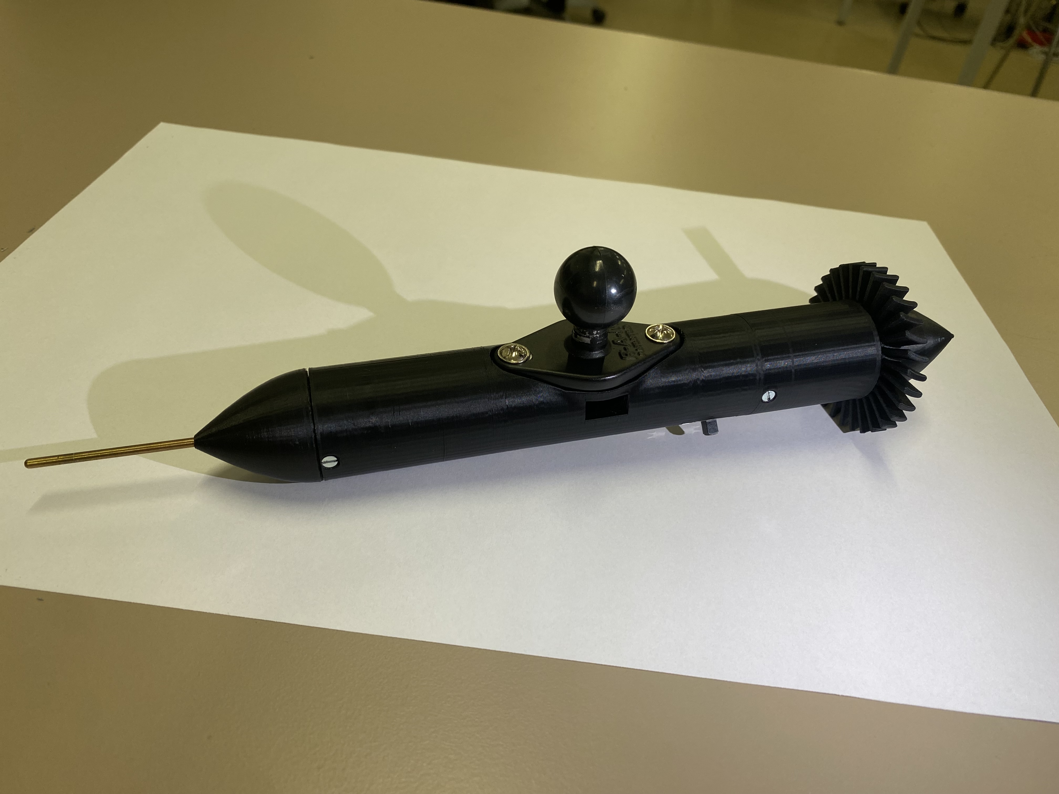
doc/Images/PhotosProjetTerminé/IMG_2862.jpg
