Belprot/2230_TubePitotDeporte_v1.0.0/doc/Images/PhotosProjetTerminé/IMG_2863.jpg

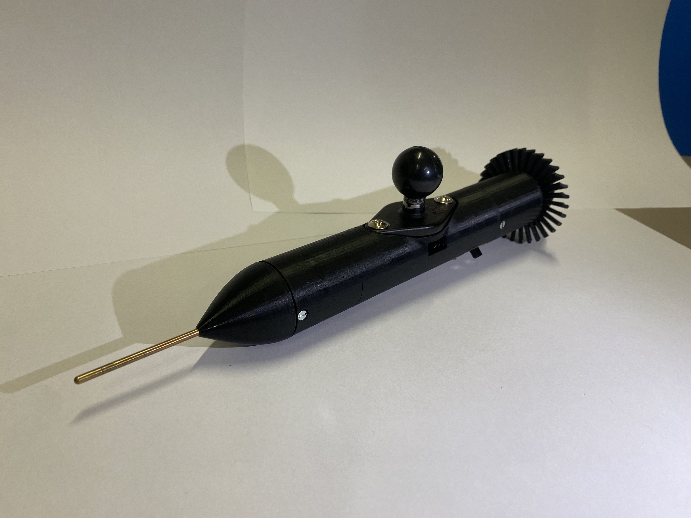
doc/Images/PhotosProjetTerminé/IMG_2863.jpg
