Belprot/2230_TubePitotDeporte_v1.0.0/doc/Images/Software/APP_STATE_INIT.jpg

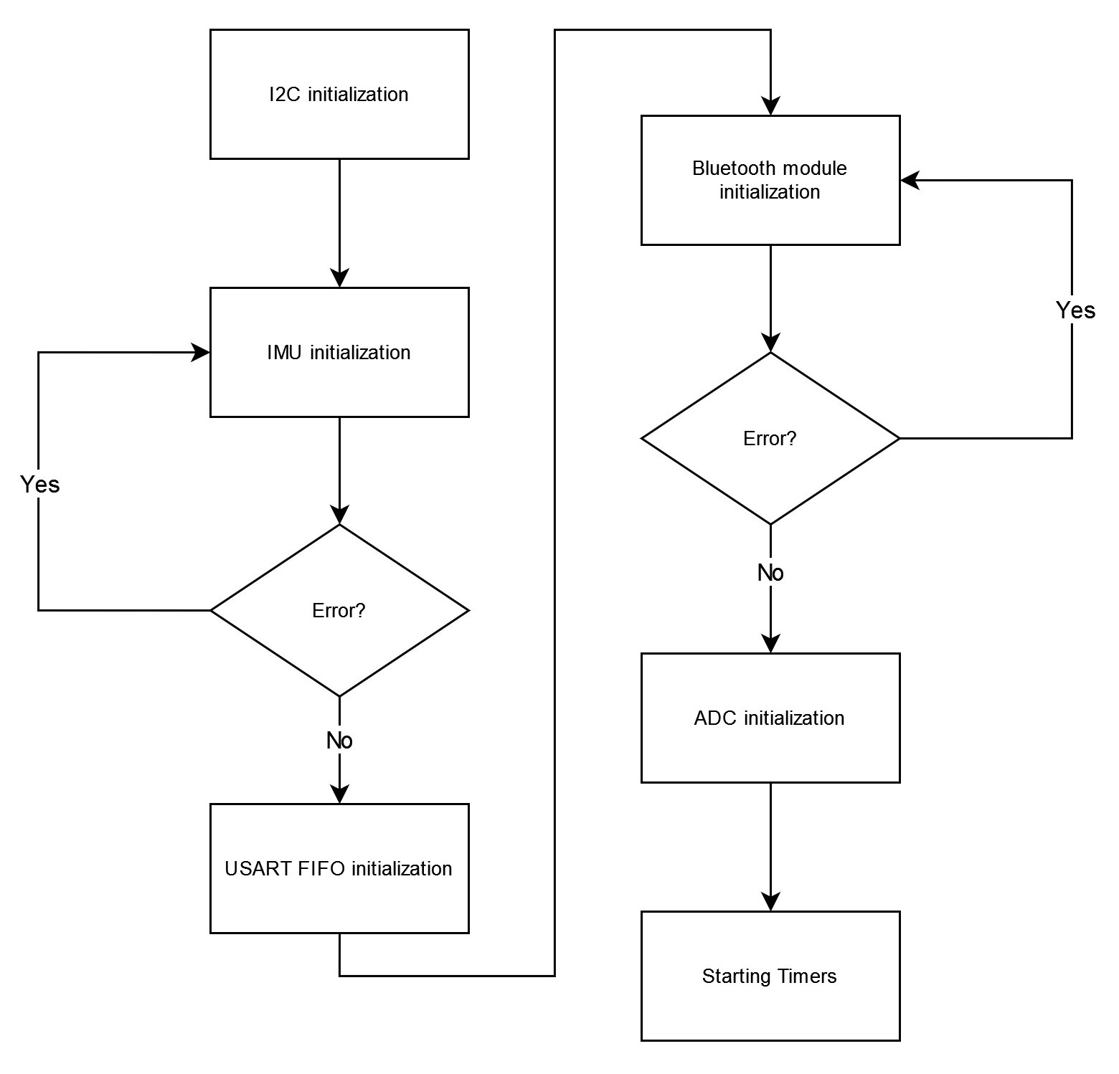
doc/Images/Software/APP_STATE_INIT.jpg
