Belprot/2230_TubePitotDeporte_v1.0.0/doc/Images/Software/Clock.PNG

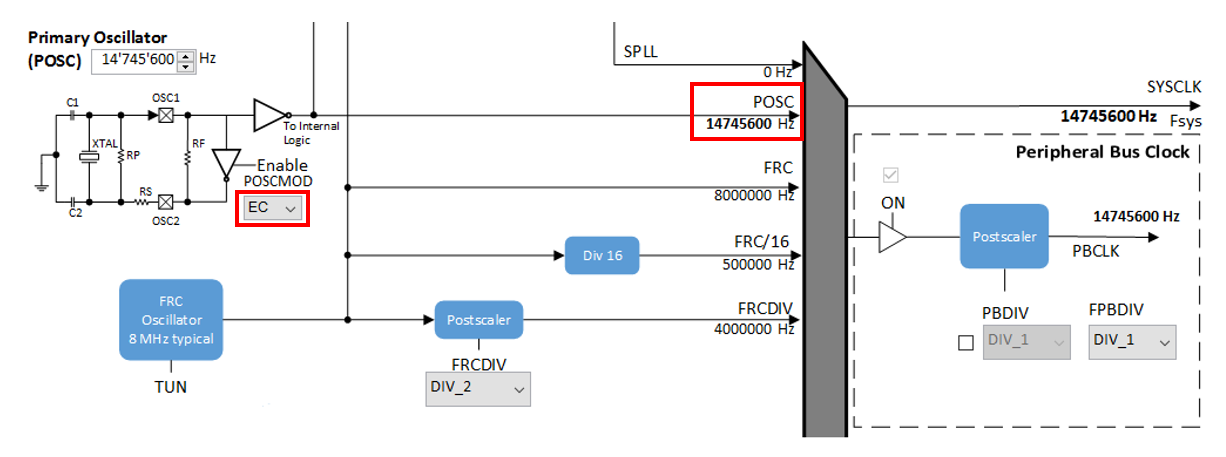
doc/Images/Software/Clock.PNG
