Belprot/2230_TubePitotDeporte_v1.0.0/doc/Images/Software/CodeCHierarchie.jpg

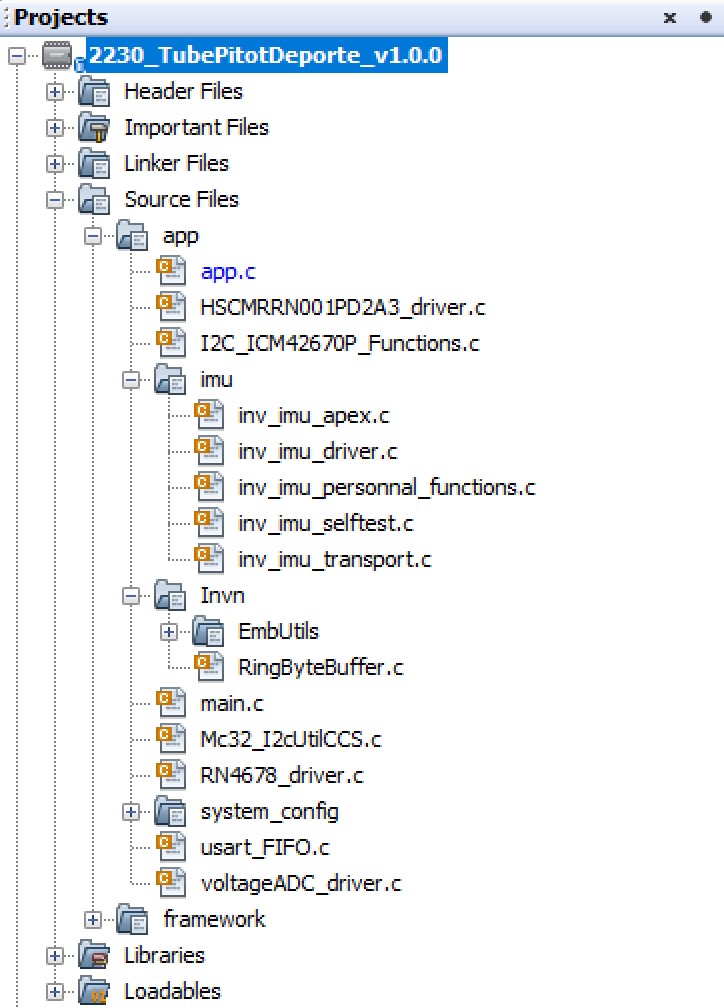
doc/Images/Software/CodeCHierarchie.jpg
