Belprot/2230_TubePitotDeporte_v1.0.0/doc/Images/Software/EntreesSorties.PNG

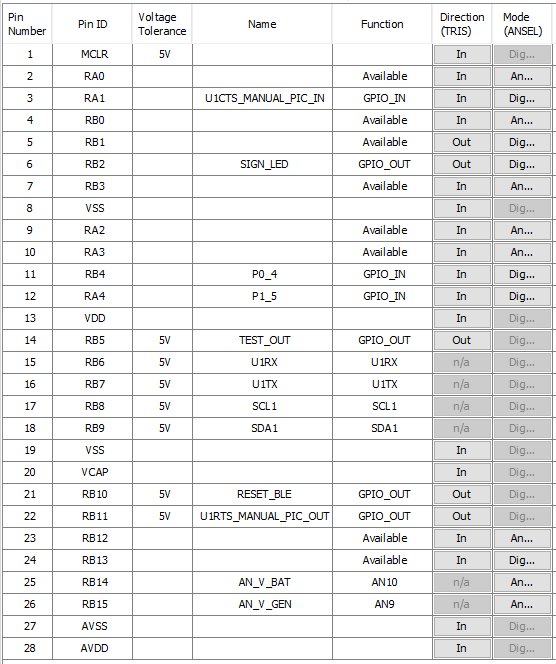
doc/Images/Software/EntreesSorties.PNG
