Belprot/2230_TubePitotDeporte_v1.0.0/doc/Images/Software/ScreenshotApp1et2.jpg

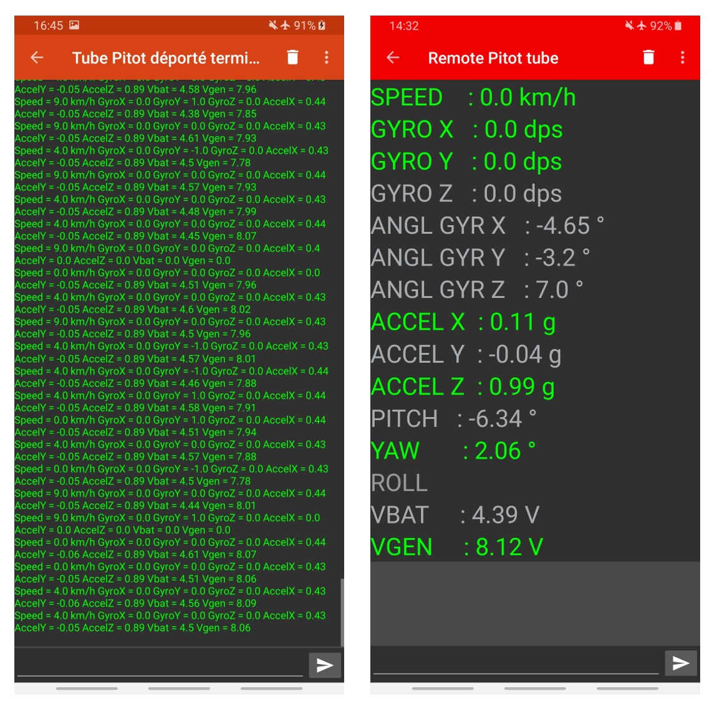
doc/Images/Software/ScreenshotApp1et2.jpg
