Belprot/2230_TubePitotDeporte_v1.0.0/doc/Images/Software/SM.jpg

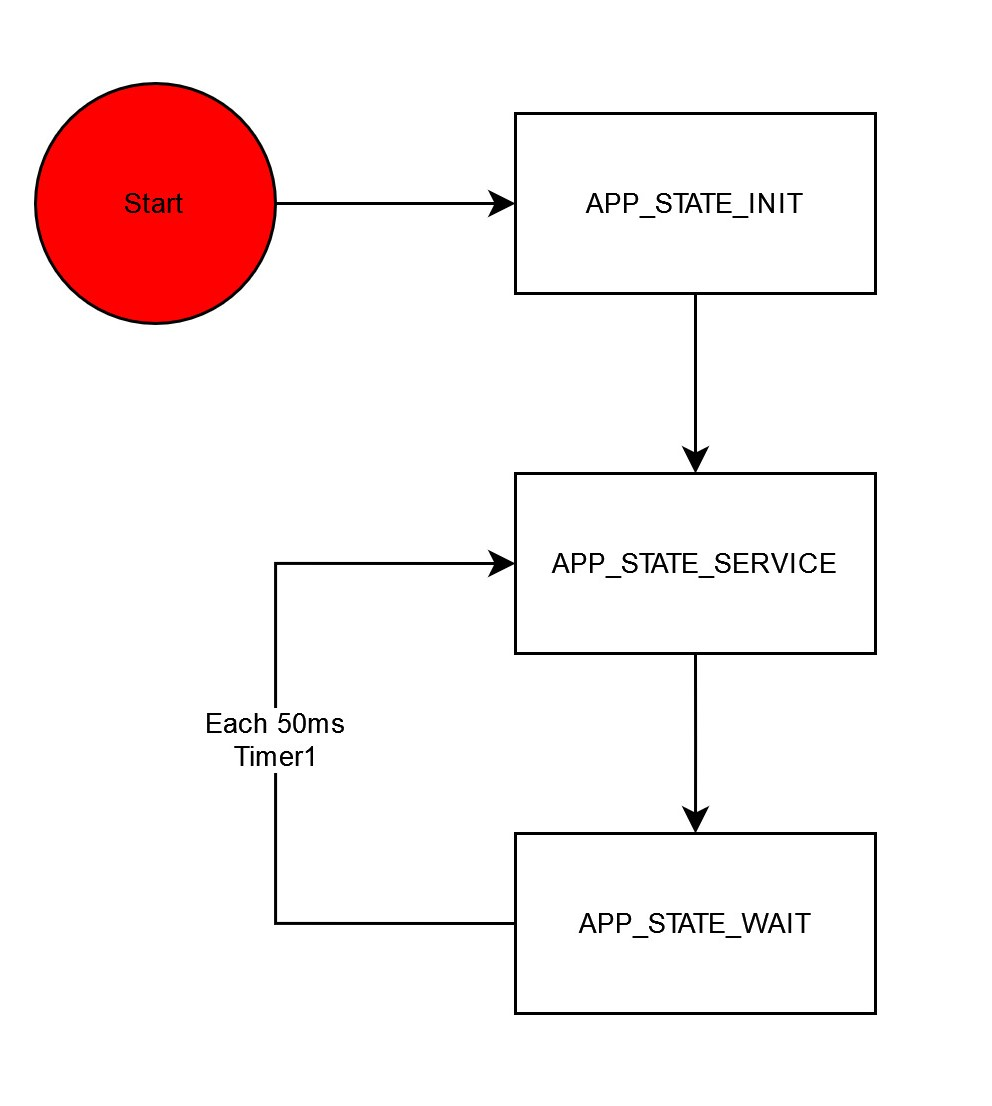
doc/Images/Software/SM.jpg
