Belprot/2230_TubePitotDeporte_v1.0.0/doc/Images/Software/USART.jpg

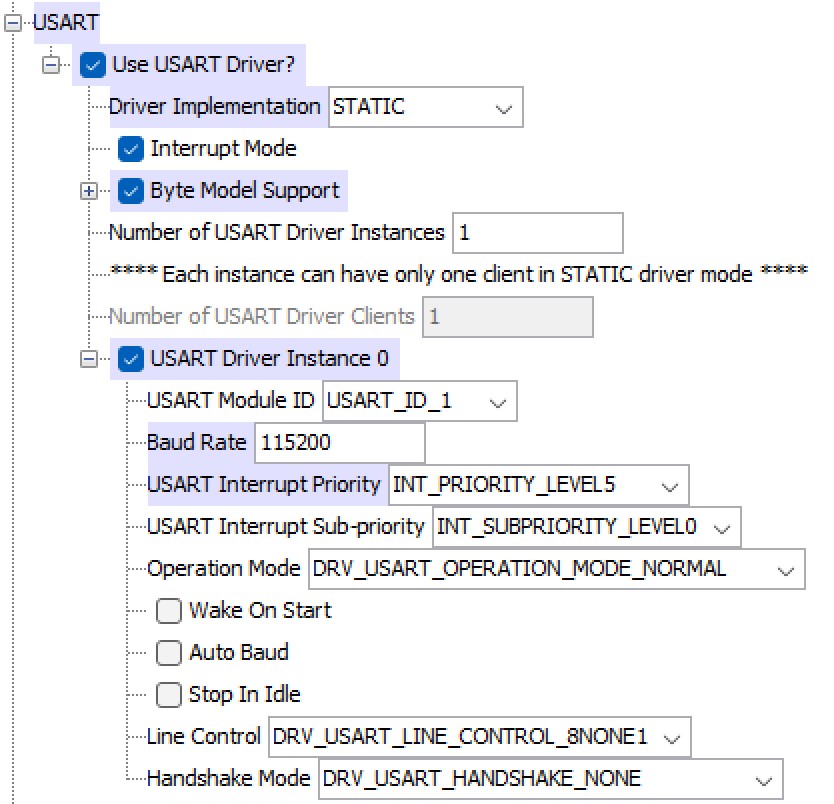
doc/Images/Software/USART.jpg
