Belprot/2230_TubePitotDeporte_v1.0.0/doc/images/DesignMecEtPCB/AssemblageCompletBat.jpg

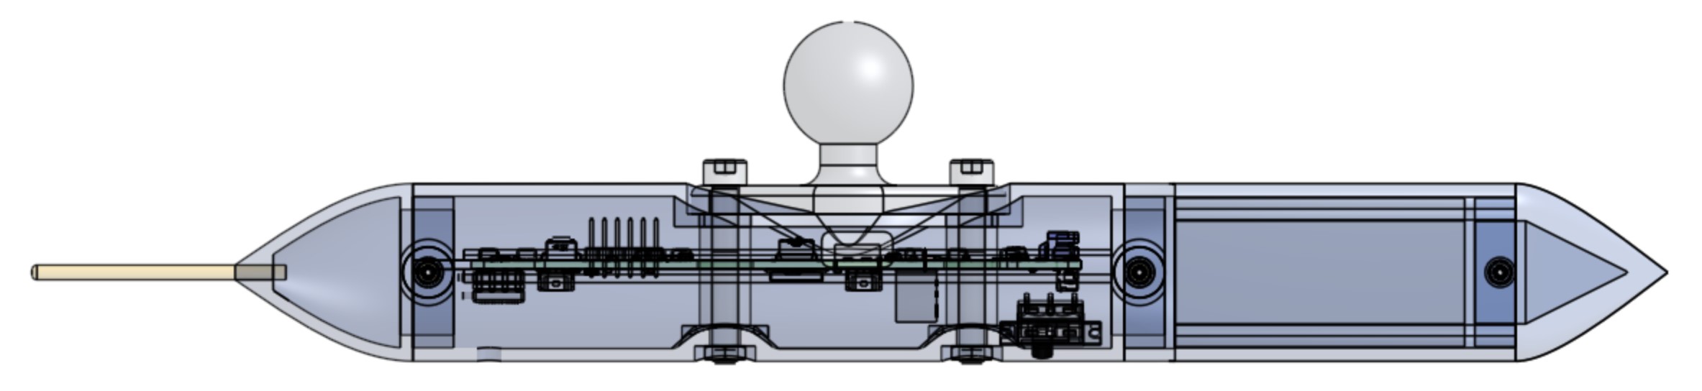
doc/images/DesignMecEtPCB/AssemblageCompletBat.jpg
