Belprot/2230_TubePitotDeporte_v1.0.0/doc/images/DesignMecEtPCB/AssemblageCompletWithNum.jpg

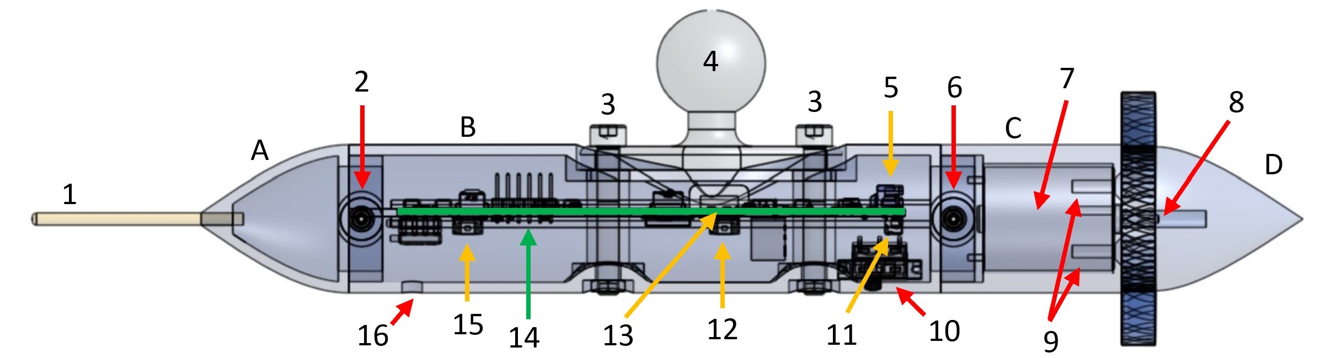
doc/images/DesignMecEtPCB/AssemblageCompletWithNum.jpg
