Belprot/2230_TubePitotDeporte_v1.0.0/doc/Images/PhotosProjetTerminé/TurbineTest.PNG

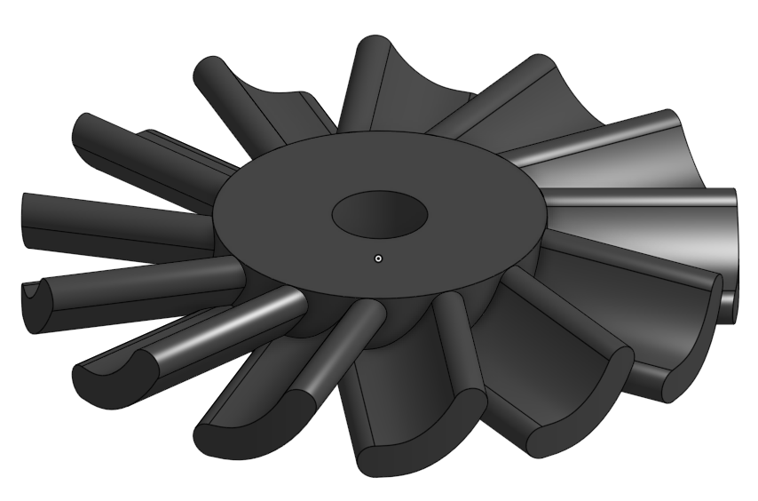
doc/Images/PhotosProjetTerminé/TurbineTest.PNG
